roechsli/Haptic-Feedback-Robot-Controller---Master-Thesis/Reports/oechslin_june/YReport_en.pdf

# Monthly Report (Yamamoto Lab.)

date: 2018.Jul.3
Author: R. Oechslin (M2)

Research theme: Haptic Feedback Controller with Palm Pressurization

— Research Plan —

Term \Month | 2 | 3 | 4 | 5 | 6 | 7 | 8 | 9 | 10 | 11 | 12 | 1

Literature review
Design PlayStation Controller
Test PlayStation Controller
Frequency Response Analysis Design Pilot Controller
Test Pilot Controller

Theoretical Analysis
Analyze data and compare
Write Thesis

— Work Contents —

### 1 Introduction

This report is the continuation of the first two reports about the project ”Haptic Feedback Controller with Palm Pressurization”. The last report has left off with the idea of implementing a voltage follower and suggested to retake measurements to create a Bode diagram. Furthermore, it has been suggested to create an analytical model and analysis of the setup in order to run simulations to identify setup parameters such as the equivalent spring constant, gain values or motor parameters.

### 2 Theoretical analysis

To come up with a theoretical analysis of the transfer function, a simplified mechanical schematic has been drawn. This schematic can be seen in figure 1. The equations of motion can be formu-


Figure 1: Simplified mechanical schematic of the actuation system with the stimulator.

lated with the major parameters defined in the schematic. A full explanation of all parameters

– 1 – | Author: R. Oechslin

can be seen in table 2. The variables with subscript 1 refer to the first mass element, the carriage in its guideway, whereas variables with subscript 2 refer to the stimulator, also known as the palm pad. For the motor the subscript m has been used.

Designator | Explanation | Unit
Tm T θm θ LCL m1 m2 x1 x2 keq bsp n kop bop JT | Motor torque Output torque acting on carriage Motor angle Clamp link angle Clamp link length Mass of the carriage in its guideway Mass of the stimulator Position of the carriage in its guideway Position of the stimulator Equivalent spring constant Spring damping coefficient Reduction gear ratio Spring constant of the operator Damping coefficient of the operator Total inertia of mechanical setup | [Nm] [Nm] [rad] [rad] [m] [kg] [kg] [m] [m] [N/m] [Ns/m] [-] [N/m] [Ns/m] [kgm² ]

Figure 2: Setup parameters

Assumptions
First of all, it is important to mention that the transfer function is non-linear, due to the motor angle θm that determines the force acting on the carriage with mass m1. As an initial approach however, this effect has been neglected. More specifically, it is assumed that θ ≪ 1 and cos (θ)

Tm
LCL

= Fcarr becomes Tm
LCL

≃ Fcarr. Here the angle θ is the angle of the lever, pushing the carriage (ie. θm = nθ).
Furthermore, there are several types of friction in the system: the intrinsic friction within the motor and its reduction gear, inside the bearings and the carriage in its guideway. Additionally the springs have a non-negligible damping coefficient. In this work the overall friction and the spring damping have been merged and are represented by the friction coefficient bsp. The stimulator, is not in contact with the controller, but with the operator. To model the damping of the skin of the operator and the friction between the skin and the palm pad, the damping coefficient bop has been introduced. Similarly the spring constant of the operator’s skin is modeled by kop.

Spring Constant and Damping Coefficient of the Operator’s Hands
The order of magnitude of the two coefficients kop and bop are discussed in [Kuchenbecker et al., 2003] [Park et al., 2014] [Speich et al., 2005]. They all indicate parameters varying in the same order of magnitude, namely kop ≃ 400N/m and bop ≃ 5Ns/m.

Identification of the Spring Damping Coefficient
The damping coefficient of the spring bsp can be found by comparing the theoretical results of the frequency response analysis with the experimental findings. In fact, for the experimental setup, the stimulator has been fully blocked and therefore the operator’s spring coefficient can be
Author: R. Oechslin | – 2 –

seen as infinitely stiff.
By varying bsp and Bode-plotting the results of the analytical transfer function, the coefficient’s order of magnitude can be found. In order to do so, the analytical transfer function has to be identified.

Expected Transfer Functions
The system can be cut into two major transfer functions. The block diagram including these two transfer functions is depicted in figure 3.

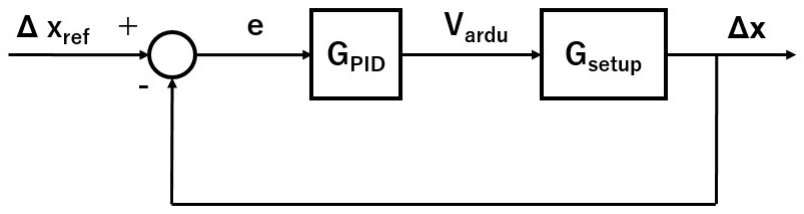
[picture p40: figure]

Figure 3: Block diagram with two different transfer functions.

According to this figure one can obtain a transfer function of the following form:

F(s) = GP ID(s)Gsetup(s) = Vardu
E

∆X

Vardu

=

∆X(s)
E(s)

(1)

where Vardu is the voltage output of the arduino for controlling the motors. Using this form one can calculate the individual transfer functions and finally relate the compression of the springs ∆x to the compression given as reference ∆xref , since ∆Xref /∆x = F/(1 + F).
PID Transfer Function The transfer function given by the PID-controller is very straightforward and can be taken out of any control theory book [Dutton et al., 1997]. Since the arduino has limited resolution with floating point operations, the error and reference has been converted into micrometers. To keep the gains consistent between the arduino code and the matlab script for analytical analysis, the multiplication factor Kµm to get from the reference distance in meters to micrometers has been introduced. Furthermore, an offset has been added (Kbit−of fset = 128) to allow for negative armature voltages and lastly the PID value has been converted to the arduino output voltage, where 255 corresponds to 5 V. The transfer function is given in equation 2.

GP ID(s) = Vardu(s)
E(s)

= (Kµm(KP +

KI
s
+ KDs) + Kbit−of fset)KP ID2V ardu | (2)

Finally, there is also the gain of the amplifier in voltage mode, which converts the voltage of the arduino into the voltage applied to the motors. This gain is Kampl = 10Volt/Volt. To this voltage an offset voltage of Vof fset = −25V is added.

Motor Equations The second transfer function relates the motor torque Tm to the arduino voltage as well as the output ∆x to Tm. Due to the back electromotive force these two parts are related and have to be treated as a whole.
The output torque Tm of the motor can be calculated using the sum of all torques and the conversion parameters intrinsic to the motor.
Similar to the setup and analysis in [Junior et al., 2016] the equations of the motor are given as:

La

dia
dt + Raia + Kemf ˙θm = Va | (3)

where La is the armature inductance, Ra the armature resistance and ia the armature current of the motor. Kemf is the back electromotive force constant also given by the motor. Va is the armature voltage and θm is the angle of the motor shaft.
Furthermore, with Newton’s law, the sum of all torques must be zero, or:

JT

¨θm −

keqLCL
n

∆x −

bspLCL
n
( ˙x2 − x˙ 1) = Tm = Kτ ia | (4)

In equation 4 the parameter JT stands for the total equivalent inertia of the motor, the clamping link and the carriage of mass m1. Kτ is the proportional current torque gain constant. The moment of inertia can either be calculated as the sum of all inertias seen by the motor shaft, or measured in a simple test.

Analytical Inertia Identification
The total inertia of the system is determined by the inertia of the rotor and gears Jm, the inertia of the clamp link JCL as well as the inertia of the carriage assembly with mass m1. The last one can be found by simplifying the load to a point mass at distance of the clamp link’s length LCL, which yields a moment of inertia of Jcarr = m1L

2
CL. The gear box affects the inertia seen by the motor shaft by the square of its ratio n:

Jref lected =

Jload
n²

(5)

We therefore have a total inertia of:

JT = Jm +

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
where JCL can be calculated by approximating it as a cantilever with an off-center axis of distance LCL/2

1
:

JCL =

1
12

mCL(A

2 + B

2 + 12l

2
) | (7)

where A and B are the width and length respectively.
The calculated total moment of inertia for the motor with a reduction ration of n = 112 is JT = 6.87 × 10−8
kgm²

Experimental Inertia Identification
Alternatively, one can approximate the total moment of inertia by applying a constant current on the motor and measuring the acceleration. In this case the traveled distance has been derivated twice to find the acceleration, which results in an amplification of errors. Furthermore, the constant current has been kept very low, (between 20 and 100 mA), which led to a slow movement and therefore higher friction impact on the measurements. However, the results are consistent with the theoretically calculated values:

JT =

7.5 × 10−4
n²

= 5.98 × 10−8
kgm²

Relating ∆X to θ

1
(2018, June 19th) retrieved from http://www.orientalmotor.com/technology/motor-sizing-calculations. html

The conversion between the angle θ and the carriage’s traveled distance x1 can be found by assuming that the horizontal displacement of the carriage is given by LCLsin(θ) = x1. For small angles of θ the Taylor expansion gives:

LCLθ ≃ x1 | (8)

The output ∆x is the compression of the springs and is given by ∆x = x2 − x1. For finding x2

the equation of motion given by Newton’s law has been considered.

m2x¨2 = −keq(x2 − x1) − bsp( ˙x2 − x˙ 1) − kopx2 − bopx˙ 2 | (9)

In the case where the stimulator has been blocked by a wall, ˙x2 has been forced to zero. Using the Laplace transform and equation 9 one finds the expression of x2:

X2 = −

keq + bsps
s

2m2 + bops + kop

∆X | (10)

Motor and Spring Transfer Function Combining all the equations one can find the final block diagram, which can be seen in figure 4

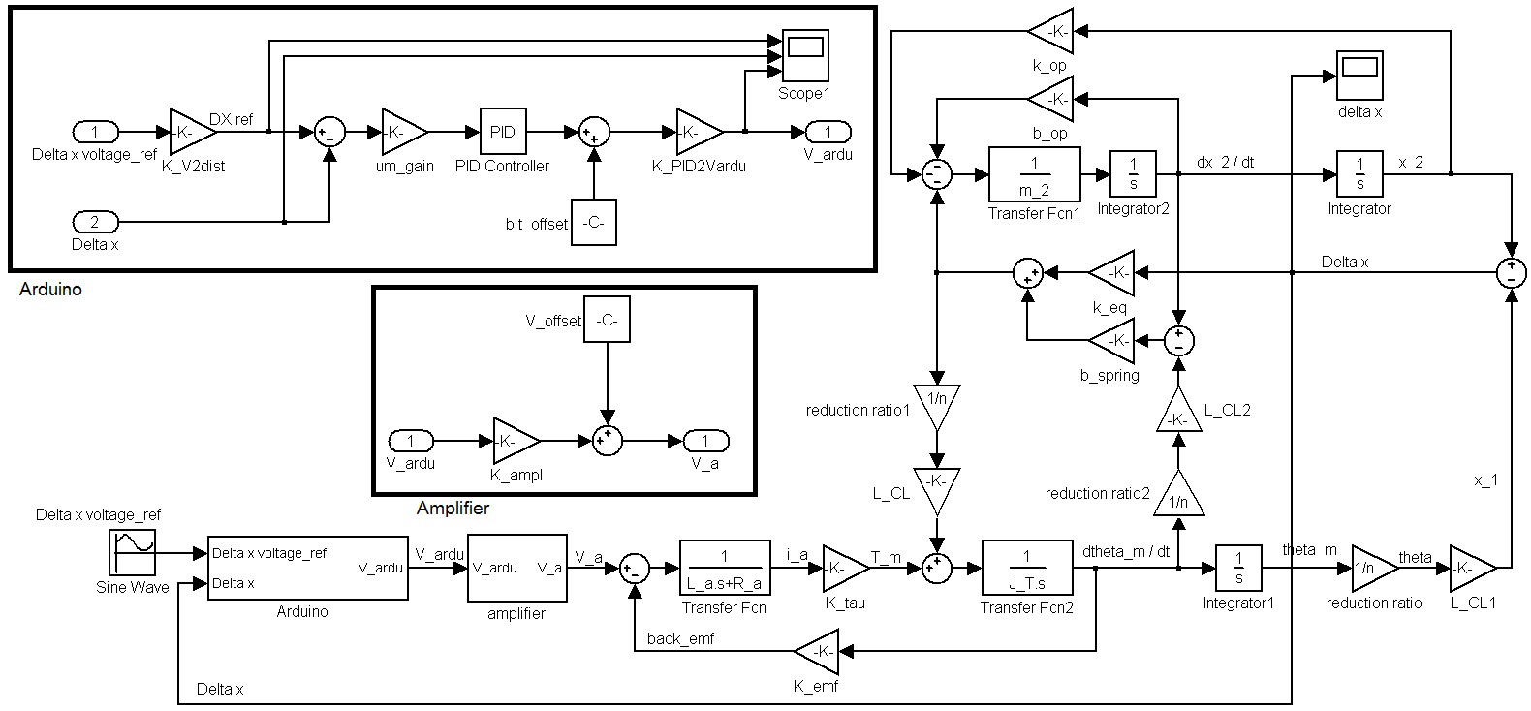
[picture p41: figure]

Figure 4: Complete block diagram relating the output ∆x to the input ∆xref .

From this diagram and the equations mentioned above, one can obtain the transfer functions that relate the output ∆x and input ∆xref as introduced in equation 1, where ∆X(s) and ∆Xref (s) are the Laplace transforms of the output and input functions respectively.
It is thus possible to study the frequency response by simulating this setup with the assumptions mentioned earlier.

Main Equations for Analytical Transfer Function

∆Xref − ∆X = E | (11)

((KP + KDs +

KI
s
)EKµm + Kbit−of fset)KP ID2V arduKampl + Vof fset = Va | (12)

Va − Kemf ˙θm

Las + Ra

Kτ + Fcoupled = JT

¨θm | (13)

Fcoupled = (keq + bsps)

LCL
n
∆X | (14)

θm =

n

LCL

X1 = −

n

LCL

(1 + keq + bsps
m2s

2 + bops + kop

)∆X | (15)

Note that the constant offsets in equation 12 are for pure symmetrical reasons and will cancel each other out, since Kbit−of fsetKP ID2V arduKampl +Vof fset = 0 and the equation becomes ((KP + KDs +

KI
s

)EKµm)KP ID2V arduKampl = Va. This is the equivalent to a standard PID form with gains K′
P

, K′

D and K′
I
In the case of the experimental setup the palm pad has been blocked and therefore x2 has been forced to be constant. The last equation becomes thus: θm = −

n
LCL

∆X.

Tracking Behavior of the P-controller
The tracking behavior of the P-controlled setup can be seen in the following figures.


Figure 5: Tracking behavior of the P-controller for 2 Hz.

Comparison of Results - P-controller and Experimental Data
The analytical transfer function has only been calculated for a specific set of spring damping coefficients bsp. The results for the uniformly spaced values between 100Ns/m and 400Ns/m are depicted in figure 7. The gains that have been used are for a P-controller, it was namely K′
P = 39.2

V
mm

. The simulation result that was closest to the experimental setup can be seen in figure 8 and the corresponding transfer function is:

∆X

∆Xref

=

1.23 × 10³
3.24 × 10−6s

3 + 6.67 × 10−2s
2 + 8.48s + 1.23 × 10³

(16)

As it can be seen in figure 8 there is a constant gain of 1 for lower frequencies and a slight resonance top becomes visible around 18Hz. The phase shift is of around −210◦
for the tested


Figure 6: Tracking behavior of the P-controller for 10 Hz.


Figure 7: Bode plot comparison of experimental data of the P-controller and analytical transfer functions for several different bsp.

frequencies, and the lag does not increase more than 45◦
for the frequencies of interest. Due to the setup constraints, the analytical results of higher frequencies have not been considered.

Motor Comparison

When one goes back to the experimental results where the two motors with different reduction gear ratios have been compared (previous report), one can conclude that the motor with the higher reduction ratio has a higher output force with a tradeoff of speed. Since one of the critical elements of the SEA system is its actuation speed, it is essential to push the boundaries as far as possible. However, the high gain frequency response in the experimental setup starts to drop at much higher frequencies than the actual operating frequency (which is given by the rather slow communication speed between the robot and the control device of fop ≃ 2 − 5 Hz).

Due to the fact that even with the stronger reduction gear motor, the springs cannot be compressed


Figure 8: Bode plot comparison of experimental data of the P-controller and analytical transfer function for bsp = 300Ns/m.

to their limits, a higher possible output force has been favored and therefore the stronger motor seems more appropriate.

Experimental PID Tuning

At first, the Ziegler Nichols tuning method has been used to identify the PID gains for the setup. However, due to the non-linear behaviour, these gains resulted in a rather poor tracking performance of the reference signal.
Since an educated tuning of the gains is the very core problem of all control engineering, a lot of different approaches exist to find optimal or sub-optimal gain values. Given the complexity of the setup, it seemed reasonable to go for the simple trial and error approach, where the gains have been tuned and the tracking performance was shown in real-time. This approach led to the following gain coefficients:
Designator | Value | Unit
K′ P K′ I K′ D | 47.6 0.124 247 | [V/mm] [V/mm/s] [Vs/mm]

Figure 9: Trial and error PID tuning.

Tracking Behavior of the PID-controller

The tracking behavior of the P-controlled setup can be seen in the following figures.

Comparison of Results - PID-controller and Experimental Data

With the gains stated in table 9, the frequency response can be measured again. This has been done for the left and right side, both using the motor with a reduction ratio of n = 112. The comparison between the analytical results from the mathematical model and the experimentally gathered data can be seen in figure 12.

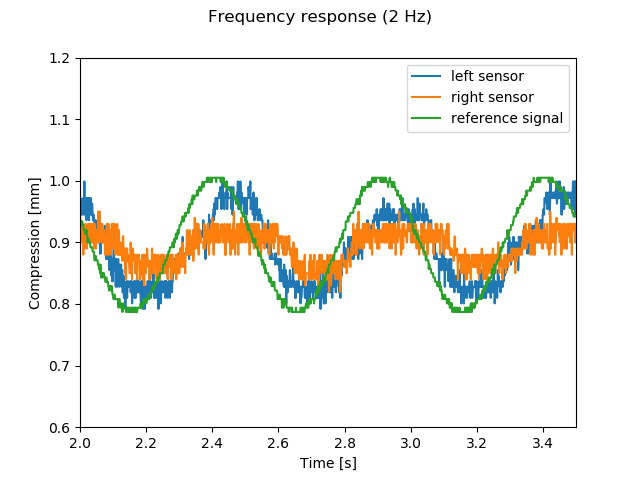
[picture p42: figure]

Figure 10: Tracking behavior of the PID-controller for 2 Hz.

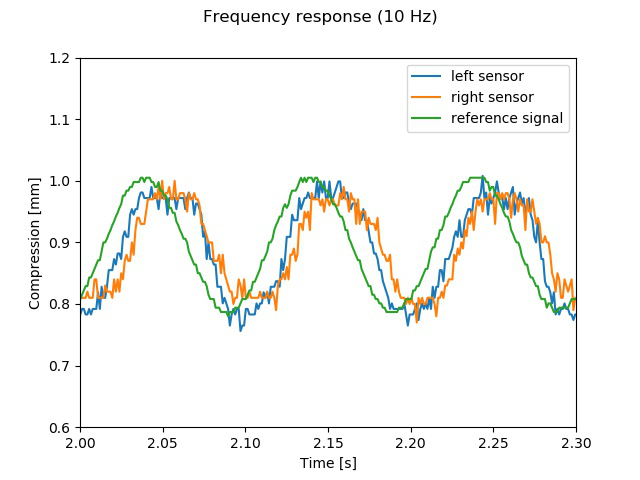
[picture p43: figure]

Figure 11: Tracking behavior of the PID-controller for 10 Hz.

### 3 Discussion

P-controlled Device
As figure 8 indicates, the results of the mathematical model seems to correspond with the experimental data. Furthermore, a damping coefficient of bsp = 300 Ns/m could be identified. The tracking behavior of this P-controller was reasonable for lower frequencies, even though there was a slight steady-state offset. The constant phase-lag was very small for small frequencies and did not exceed 45◦
for frequencies up to 10 Hz. Even an approach of discretizing the analytical results did not yield a better match of the results.

PID-controlled Device
When the PID-controller has been implemented, the difference between analytical results and the experiments was much bigger. First it was noteworthy, that the two motors showed a different behavior with the same gains. This might stem from several asymmetries in the setup. First of


Figure 12: Bode plot comparison of experimental data of the PID-controller and analytical transfer function for bsp = 100Ns/m.

all and most importantly, the distance sensors are different, and have different threshold values. Also, the springs might not have been glued in a perfectly symmetrical manner. However, the noise characteristics of the sensors are in a similar order of magnitude and do not account for the differences here. Lastly, there are the mechanical aspects of how the motors have been screwed to the controller. Due to the high-frequency driving, the screws loosen from time to time, which can have a significant impact on the Bode plots. Furthermore, there might be a slight misalignment of the motor shaft axis and the guideway, which results in an opposing force.
Again, the discretization of the analytical transfer function did not yield a better match between the analytical and experimental data.
Judging from the frequency response seen in figure 12 the tracking is relatively bad at low frequencies, not only because there is an attenuation, but also that the resonance top at higher frequencies quickly leads to saturation of the applicable motor voltage. In addition to this, the phase lag is much bigger and is already at least 45◦
in the lower range of the bandwidth. This is due to the filters that have been used. The first filter is an RC-circuit that takes the PWM signal from the arduino and produces a more continuous voltage signal for the amplifiers. The cut-off frequency is 330 Hz. The second filter is within the arduino code and is used to filter the measured distance. This filter was necessary to reduces the impact of noise amplification in the derivative part of the PID-controller. Three different filters with cut-off frequencies from f1 = 1.6 Hz, f2 = 4.2 Hz and f3 = 8.8 Hz have been tested.

### 4 Conclusion

Given the results for the P-controller, one can assume that the mathematical model is correct. However, when one implements a PID-controller, a higher discrepancy between mathematical model and experimental data arises. Even though the parameters used in the mathematical model have been double-checked (such as the moment of inertia for example), its validity can be questioned.
From the two different implementations, the P-controller shows a better tracking behavior for the operational bandwidth.

### 5 Outlook

In the future, the P- and PID-controller shall be tested and a subjective measure of the feedbacks smoothness and transparency shall be reported.
A more thorough literature shall be done to discuss the findings with existing papers.
A design-choice guide shall be created in order to facilitate future research for similar setups.

References

[Dutton et al., 1997] Dutton, K., Thompson, S., and Barraclough, B. (1997). The art of control engineering. Addison Wesley Harlow.

[Junior et al., 2016] Junior, A. G. L., de Andrade, R. M., and Bento Filho, A. (2016). Series elastic actuator: Design, analysis and comparison. In Recent Advances in Robotic Systems. InTech.

[Kuchenbecker et al., 2003] Kuchenbecker, K. J., Park, J. G., and Niemeyer, G. (2003). Characterizing the human wrist for improved haptic interaction. In ASME 2003 International Mechanical Engineering Congress and Exposition, pages 591–598. American Society of Mechanical Engineers.

[Park et al., 2014] Park, J., Paˇzin, N., Friedman, J., Zatsiorsky, V. M., and Latash, M. L. (2014). Mechanical properties of the human hand digits: Age-related differences. Clinical Biomechanics, 29(2):129–137.

[Speich et al., 2005] Speich, J. E., Shao, L., and Goldfarb, M. (2005). Modeling the human hand as it interacts with a telemanipulation system. Mechatronics, 15(9):1127–1142.
