roechsli/Haptic-Feedback-Robot-Controller---Master-Thesis/3D designs/Game Controller/figures/PS_controller_smaller.jpg

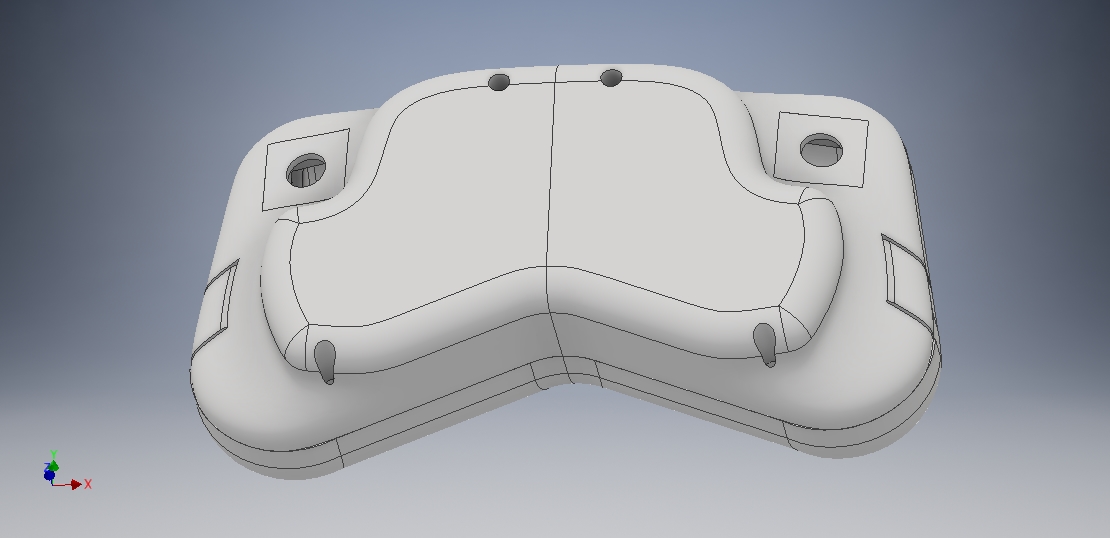
3D designs/Game Controller/figures/PS_controller_smaller.jpg
