roechsli/Haptic-Feedback-Robot-Controller---Master-Thesis/3D designs/Yoke Controller/figures/left_hand_joystick_cam_open_rend.jpg

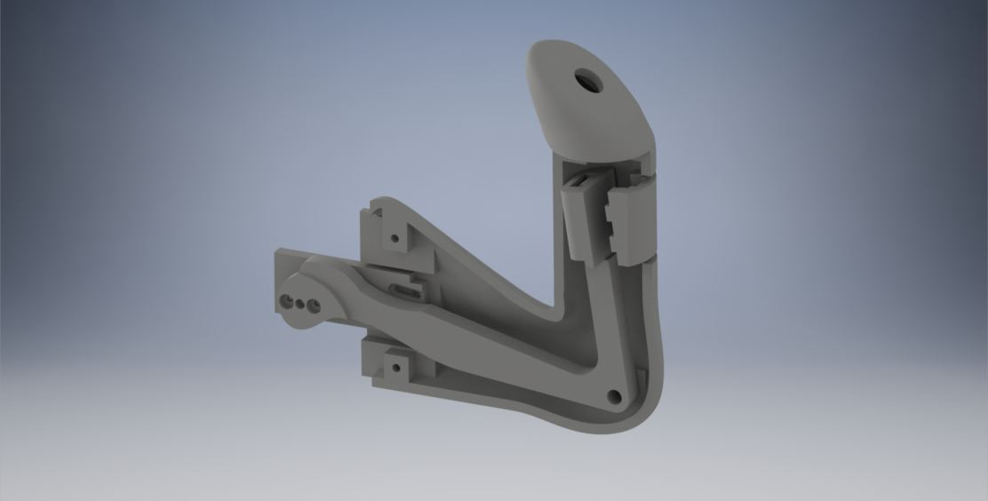
3D designs/Yoke Controller/figures/left_hand_joystick_cam_open_rend.jpg
