roechsli/Haptic-Feedback-Robot-Controller---Master-Thesis/Data/frequency_response/20180525_fra_logs/figs/f2/2plot_zoom.jpg

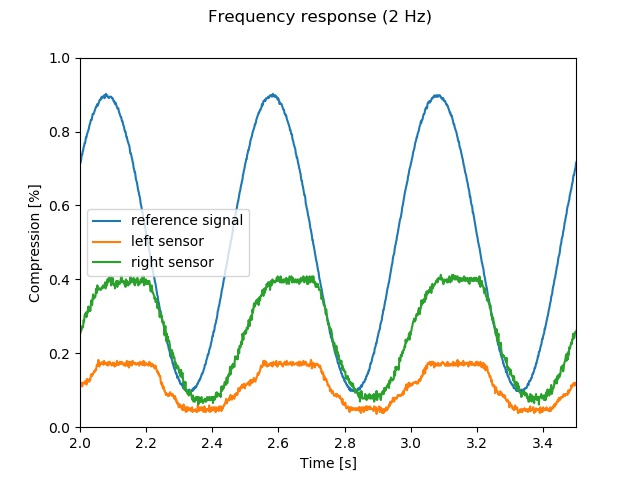
Data/frequency_response/20180525_fra_logs/figs/f2/2plot_zoom.jpg
