roechsli/Haptic-Feedback-Robot-Controller---Master-Thesis/Data/frequency_response/20180525_fra_logs/figs/f6.3/6.3plot_zoom_fixed_time.jpg

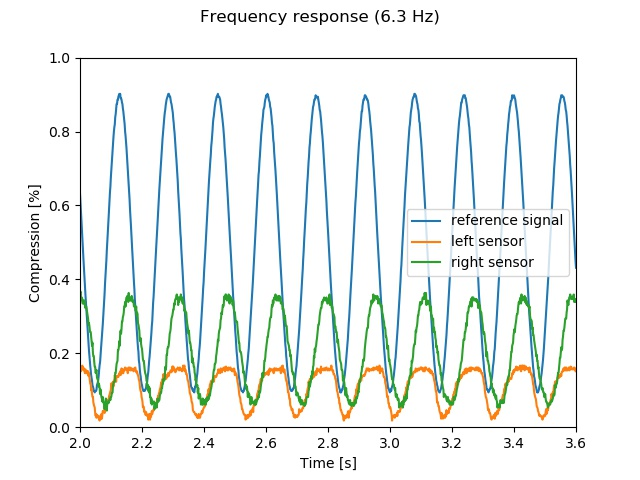
Data/frequency_response/20180525_fra_logs/figs/f6.3/6.3plot_zoom_fixed_time.jpg
