roechsli/Haptic-Feedback-Robot-Controller---Master-Thesis/Data/frequency_response/20180529_fra_logs/figs/f1.6/1.6plot_zoom.jpg

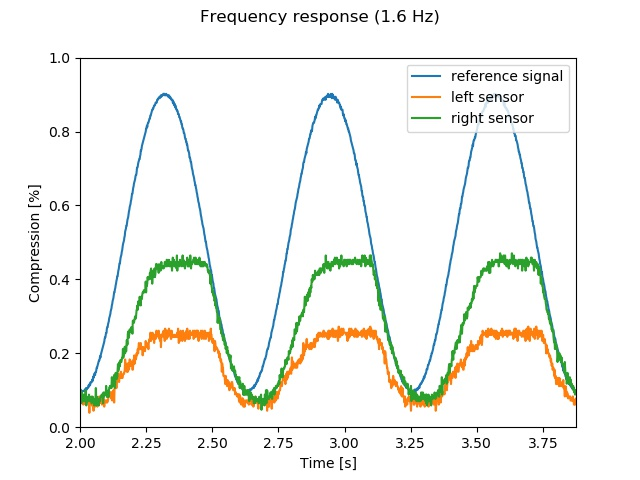
Data/frequency_response/20180529_fra_logs/figs/f1.6/1.6plot_zoom.jpg
