roechsli/Haptic-Feedback-Robot-Controller---Master-Thesis/Data/frequency_response/20180529_fra_logs/figs/f16/16plot_zoom.jpg

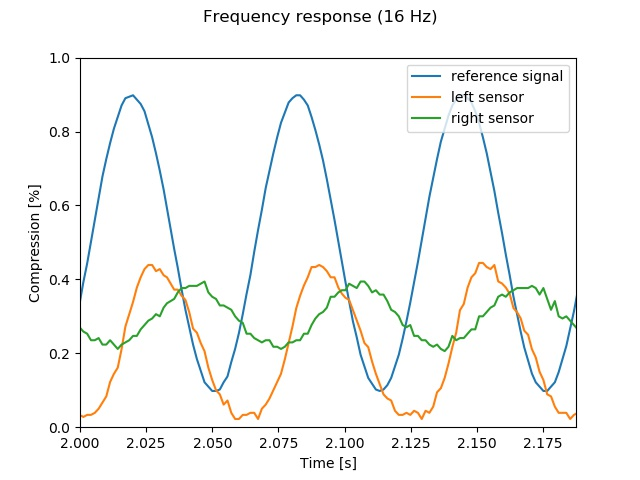
Data/frequency_response/20180529_fra_logs/figs/f16/16plot_zoom.jpg
