roechsli/Haptic-Feedback-Robot-Controller---Master-Thesis/Data/frequency_response/20180621_fra_logs/figs/bode_right.jpg

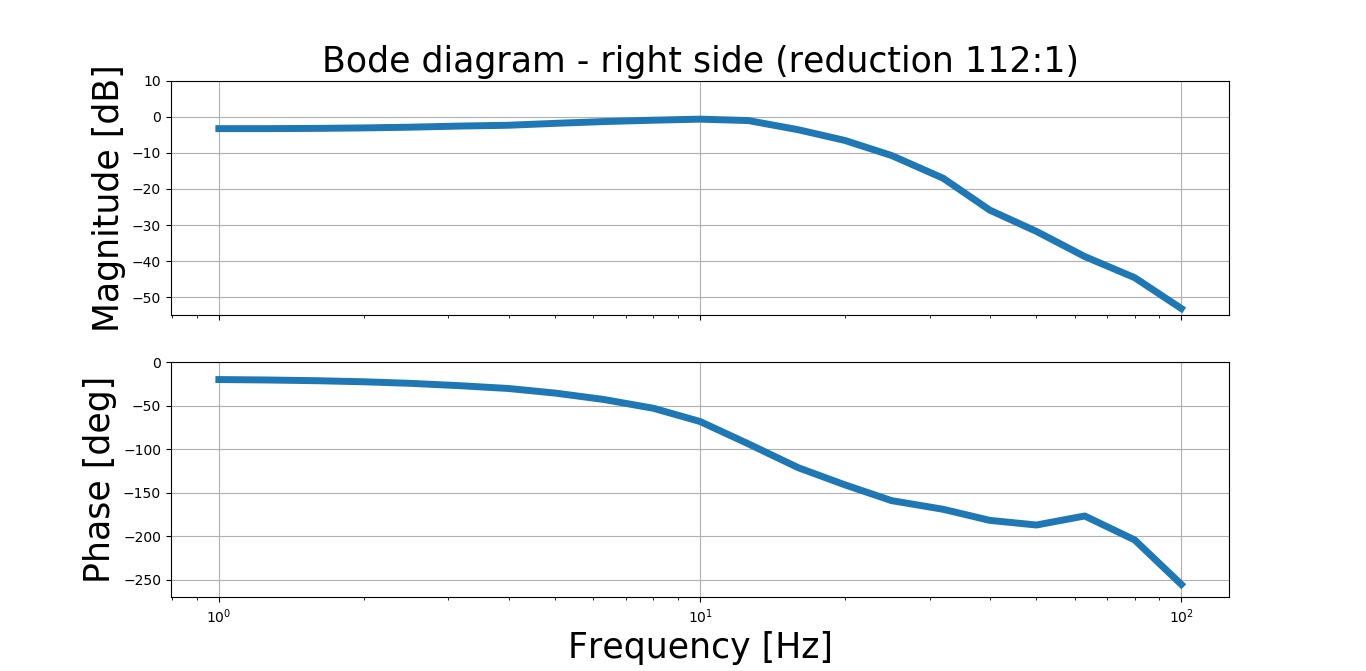
Data/frequency_response/20180621_fra_logs/figs/bode_right.jpg
