roechsli/Haptic-Feedback-Robot-Controller---Master-Thesis/Data/frequency_response/20180621_fra_logs/figs/f32/32plot_zoom_fixed_time.jpg

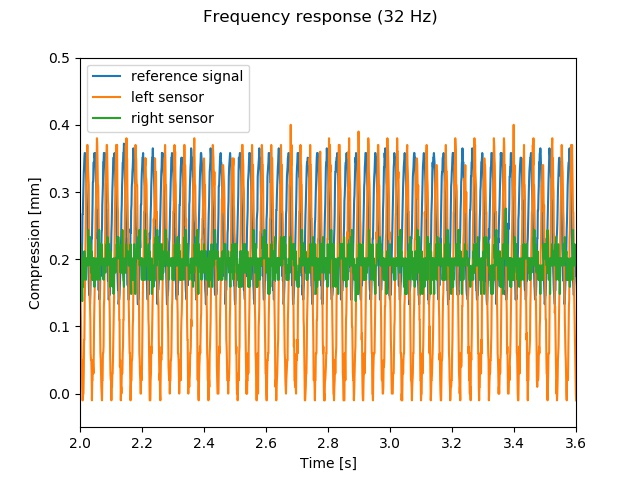
Data/frequency_response/20180621_fra_logs/figs/f32/32plot_zoom_fixed_time.jpg
