roechsli/Haptic-Feedback-Robot-Controller---Master-Thesis/Data/frequency_response/20180621_fra_logs/figs/f80/80plot_zoom_fixed_time.jpg

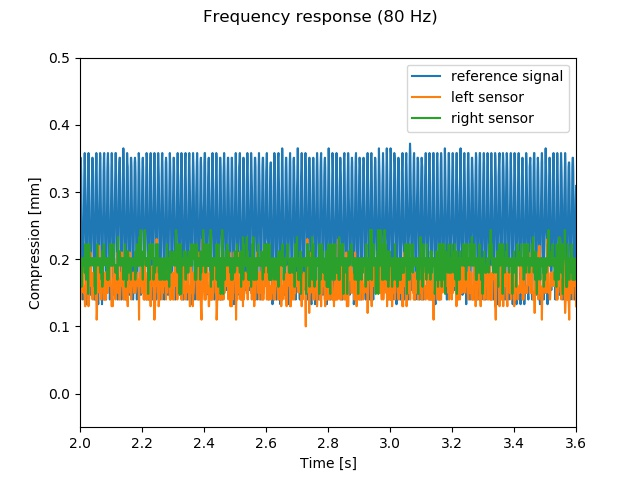
Data/frequency_response/20180621_fra_logs/figs/f80/80plot_zoom_fixed_time.jpg
