roechsli/Haptic-Feedback-Robot-Controller---Master-Thesis/Data/frequency_response/20180626_fra_logs_pid_impl/figs/f1.6/1.6plot_zoom.jpg

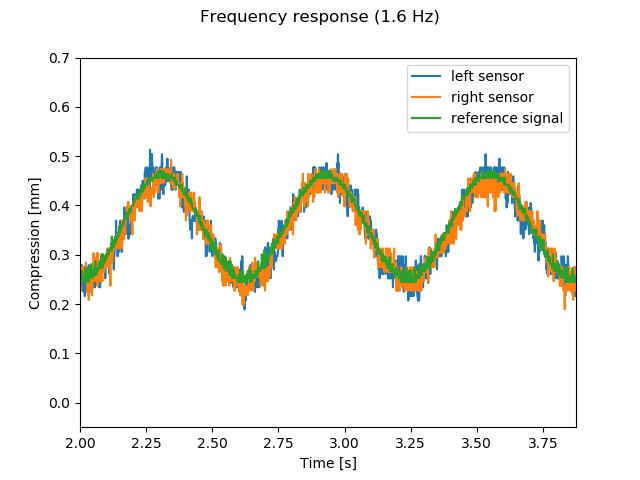
Data/frequency_response/20180626_fra_logs_pid_impl/figs/f1.6/1.6plot_zoom.jpg
