roechsli/Haptic-Feedback-Robot-Controller---Master-Thesis/Data/frequency_response/20180626_fra_logs_pid_impl/figs/f3.17/3.17plot_zoom.jpg

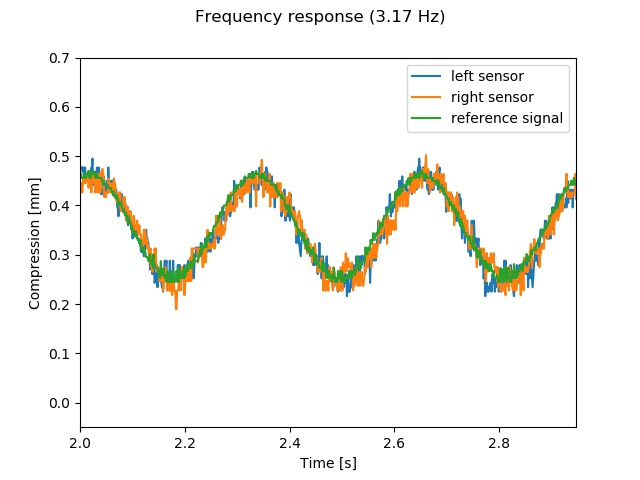
Data/frequency_response/20180626_fra_logs_pid_impl/figs/f3.17/3.17plot_zoom.jpg
