roechsli/Haptic-Feedback-Robot-Controller---Master-Thesis/Data/frequency_response/20180626_fra_logs_pid_impl/figs/f4/4plot_zoom.jpg

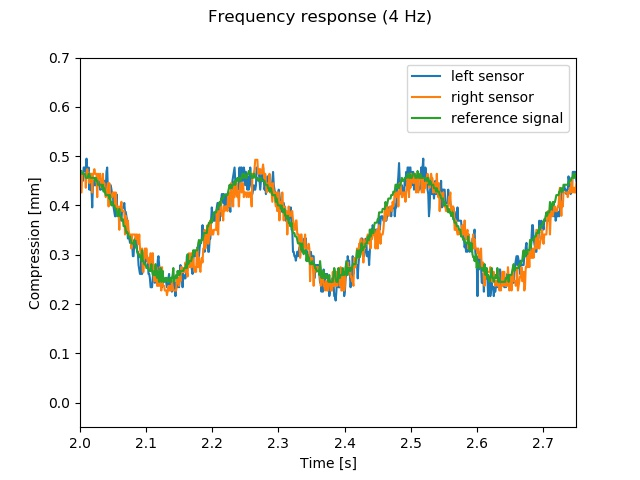
Data/frequency_response/20180626_fra_logs_pid_impl/figs/f4/4plot_zoom.jpg
