roechsli/Haptic-Feedback-Robot-Controller---Master-Thesis/Data/frequency_response/20180626_fra_logs_pid_impl/figs/f12.6/12.6plot_zoom_fixed_time.jpg

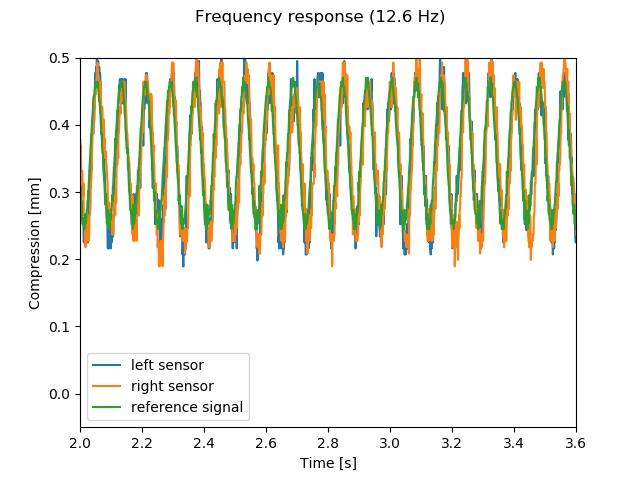
Data/frequency_response/20180626_fra_logs_pid_impl/figs/f12.6/12.6plot_zoom_fixed_time.jpg
