roechsli/Haptic-Feedback-Robot-Controller---Master-Thesis/Data/frequency_response/20180626_fra_logs_pid_impl/figs/f32/32plot_zoom_fixed_time.jpg

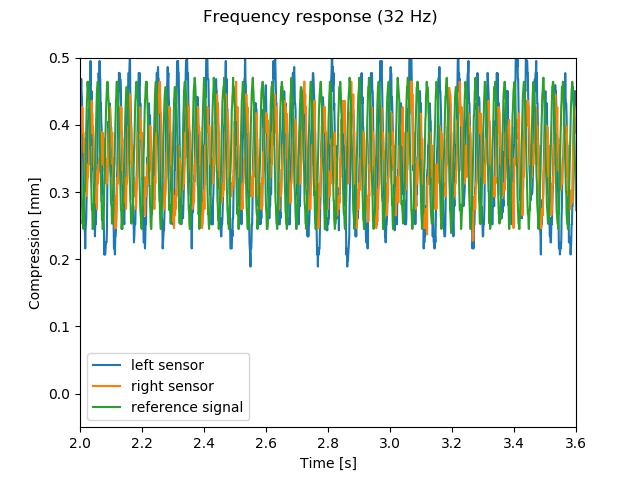
Data/frequency_response/20180626_fra_logs_pid_impl/figs/f32/32plot_zoom_fixed_time.jpg
