roechsli/Haptic-Feedback-Robot-Controller---Master-Thesis/Data/frequency_response/20180629_fra_logs_p_02/figs/bode_both.jpg

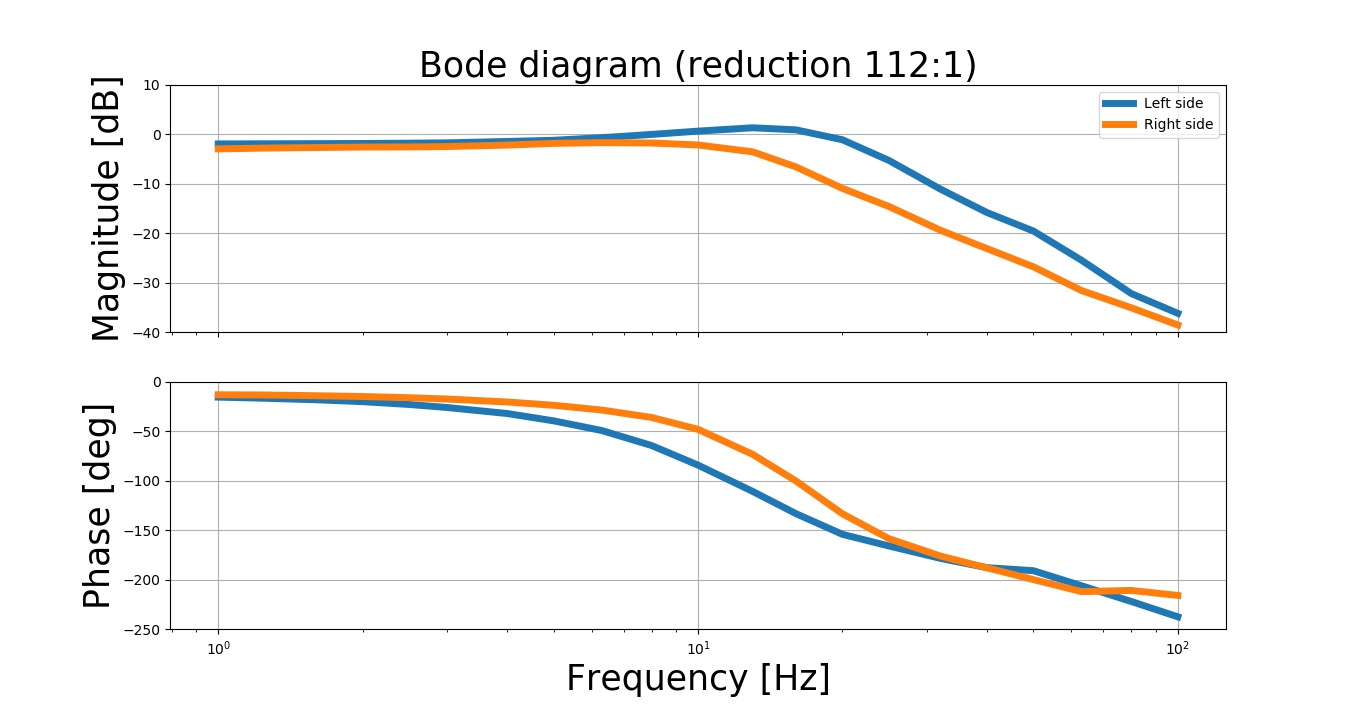
Data/frequency_response/20180629_fra_logs_p_02/figs/bode_both.jpg
