roechsli/Haptic-Feedback-Robot-Controller---Master-Thesis/Data/frequency_response/20180629_fra_logs_p_02/figs/f10/10plot_zoom_fixed_time.jpg

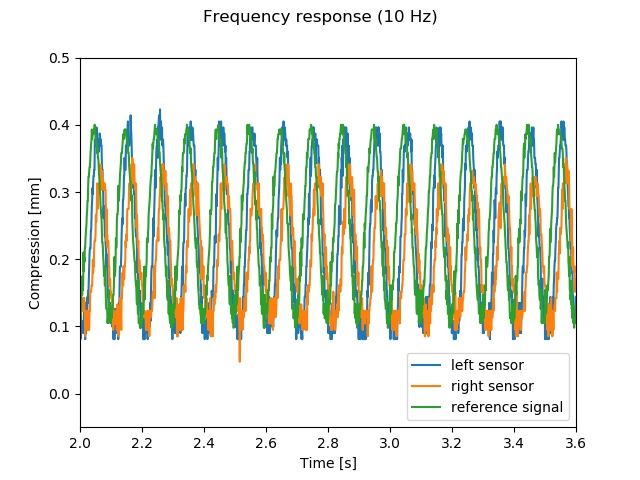
Data/frequency_response/20180629_fra_logs_p_02/figs/f10/10plot_zoom_fixed_time.jpg
