roechsli/Haptic-Feedback-Robot-Controller---Master-Thesis/Data/frequency_response/20180629_fra_logs_p_02/figs/f25/25plot_zoom_fixed_time.jpg

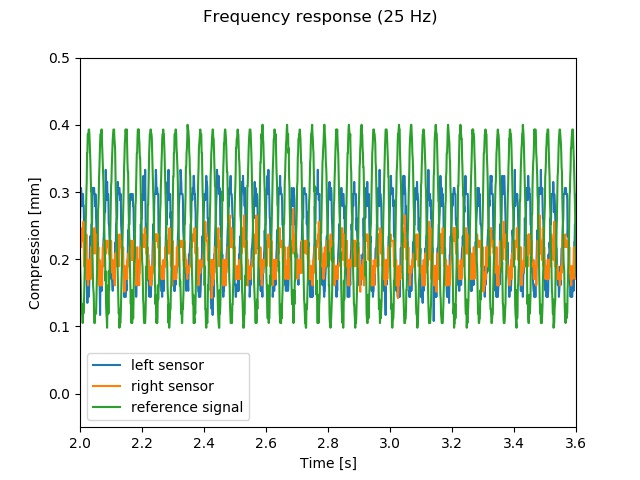
Data/frequency_response/20180629_fra_logs_p_02/figs/f25/25plot_zoom_fixed_time.jpg
