roechsli/Haptic-Feedback-Robot-Controller---Master-Thesis/Data/frequency_response/20180629_fra_logs_p_02/figs/f80/80plot_zoom.jpg

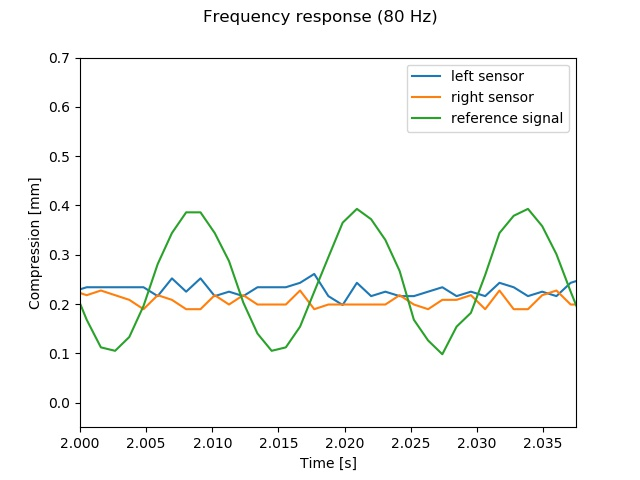
Data/frequency_response/20180629_fra_logs_p_02/figs/f80/80plot_zoom.jpg
