roechsli/Haptic-Feedback-Robot-Controller---Master-Thesis/Data/frequency_response/20180703_fra_logs_PID_243_63_00126/figs/bode_right_pid.jpg

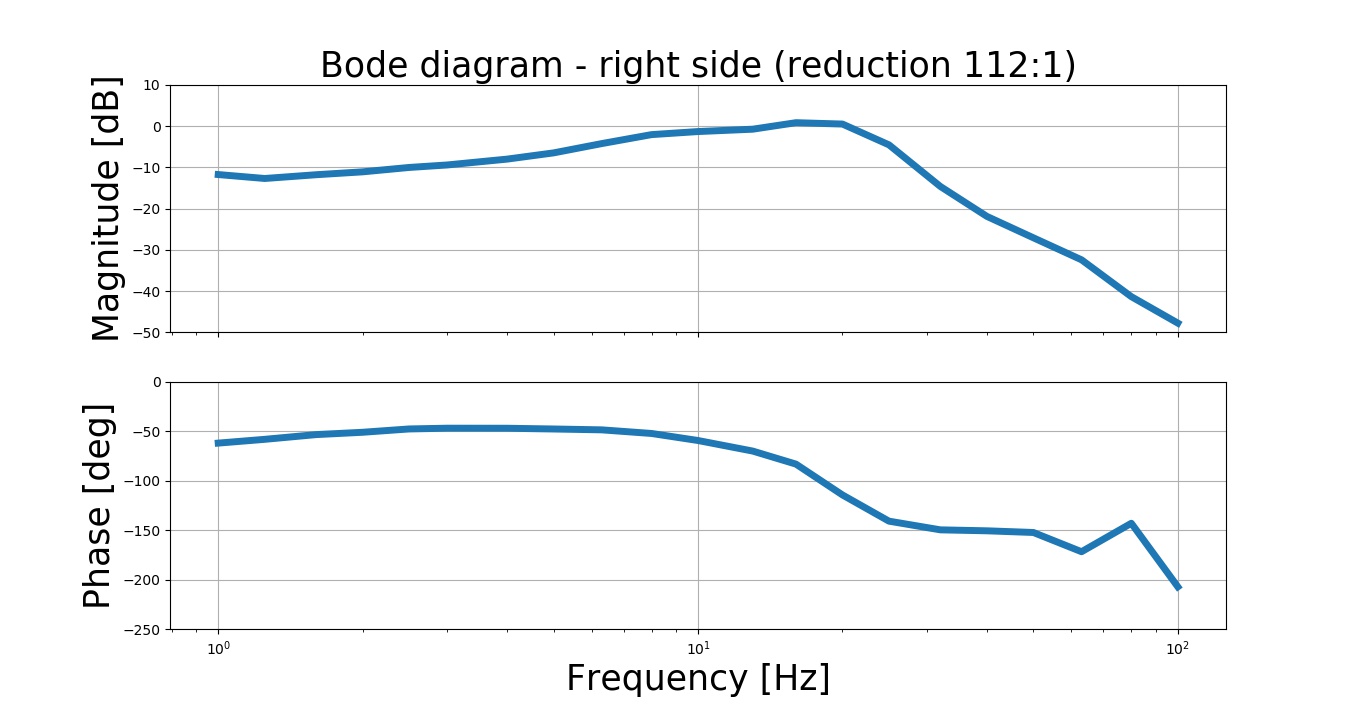
Data/frequency_response/20180703_fra_logs_PID_243_63_00126/figs/bode_right_pid.jpg
