roechsli/Haptic-Feedback-Robot-Controller---Master-Thesis/Data/frequency_response/20180704_fra_logs_PID_243_63_00126/figs/f8/8plot_zoom_fixed_time.jpg

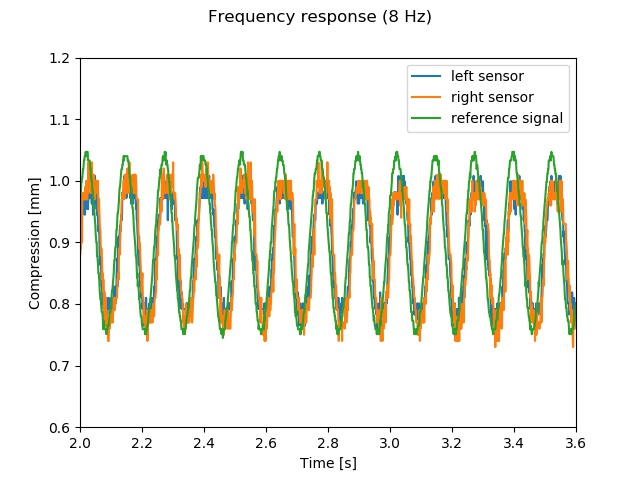
Data/frequency_response/20180704_fra_logs_PID_243_63_00126/figs/f8/8plot_zoom_fixed_time.jpg
