roechsli/Haptic-Feedback-Robot-Controller---Master-Thesis/Data/frequency_response/20180704_fra_logs_PID_243_63_00126_10perc/figs/f1.25/1.25plot_zoom.jpg

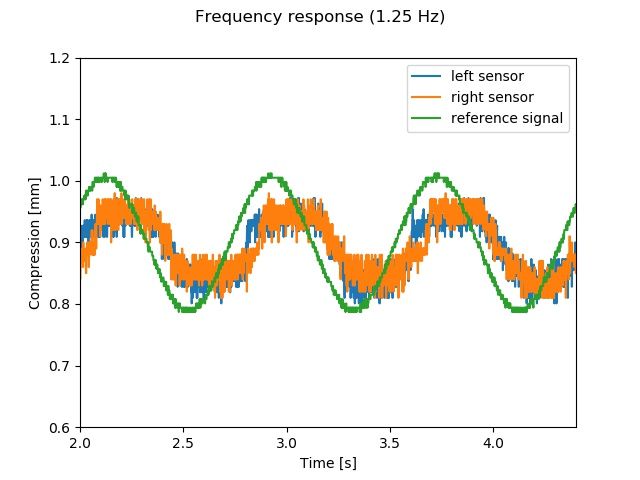
Data/frequency_response/20180704_fra_logs_PID_243_63_00126_10perc/figs/f1.25/1.25plot_zoom.jpg
