roechsli/Haptic-Feedback-Robot-Controller---Master-Thesis/Data/frequency_response/20180719_fra_logs_pilot_P02/figs/f5/5plot_zoom_fixed_time.jpg

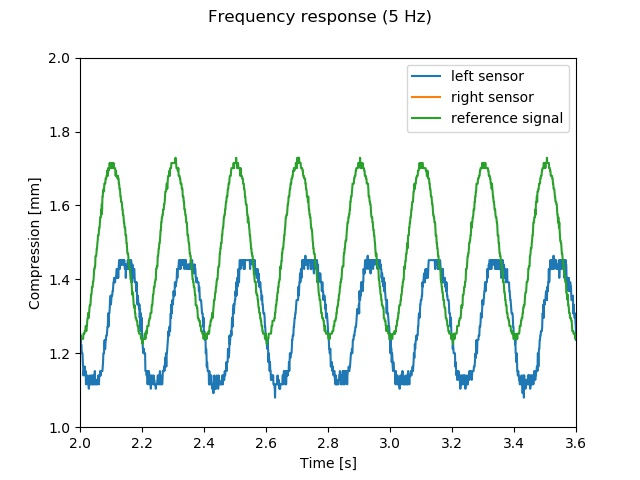
Data/frequency_response/20180719_fra_logs_pilot_P02/figs/f5/5plot_zoom_fixed_time.jpg
