roechsli/Haptic-Feedback-Robot-Controller---Master-Thesis/Data/frequency_response/20180719_fra_logs_pilot_P02/figs/f6.3/6.3plot_zoom_fixed_time.jpg

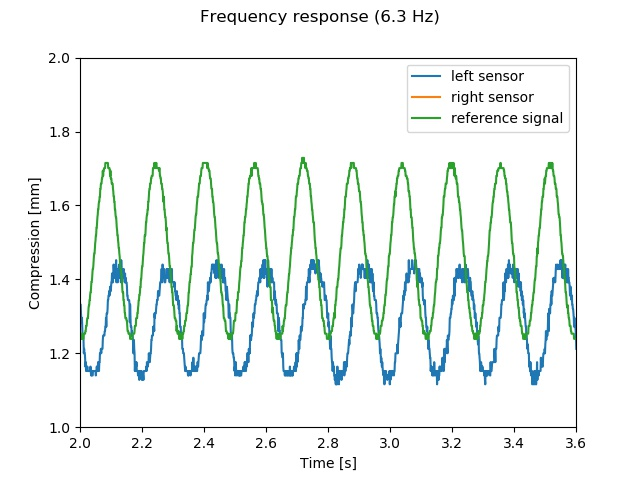
Data/frequency_response/20180719_fra_logs_pilot_P02/figs/f6.3/6.3plot_zoom_fixed_time.jpg
