roechsli/Haptic-Feedback-Robot-Controller---Master-Thesis/Data/frequency_response/20180719_fra_logs_pilot_P02/figs/f32/32plot_zoom.jpg

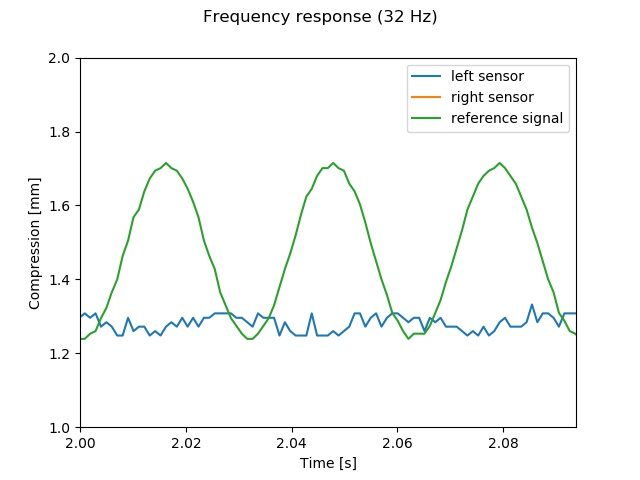
Data/frequency_response/20180719_fra_logs_pilot_P02/figs/f32/32plot_zoom.jpg
