roechsli/Haptic-Feedback-Robot-Controller---Master-Thesis/Data/frequency_response/20180726_fra_logs_pilot_P01_saturated2/figs/f6.3/6.3plot_zoom.jpg

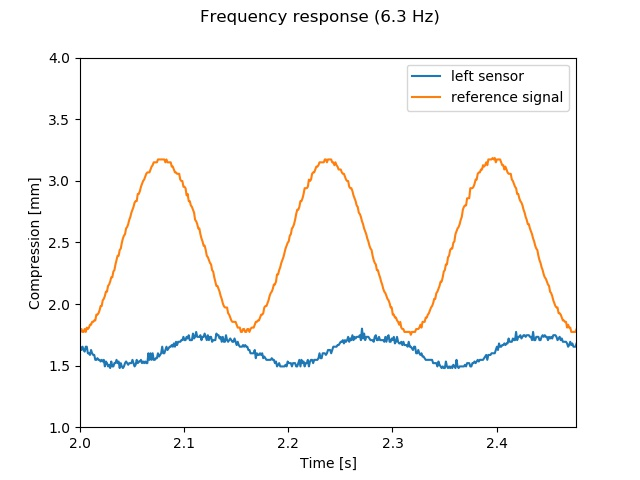
Data/frequency_response/20180726_fra_logs_pilot_P01_saturated2/figs/f6.3/6.3plot_zoom.jpg
