roechsli/Haptic-Feedback-Robot-Controller---Master-Thesis/Data/frequency_response/20180726_fra_logs_pilot_P01_saturated2/figs/f13/13plot_zoom_fixed_time.jpg

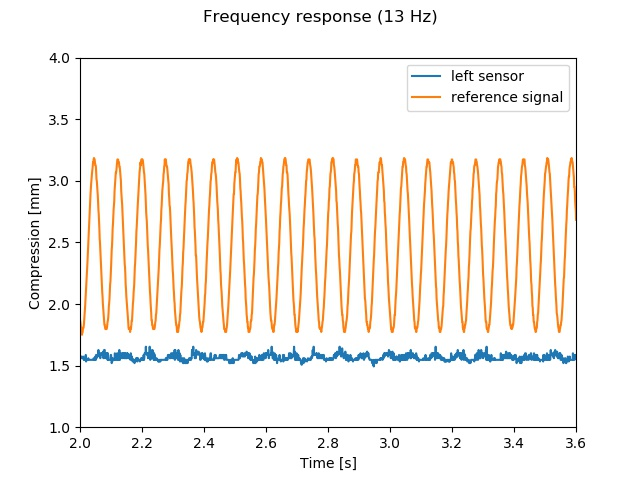
Data/frequency_response/20180726_fra_logs_pilot_P01_saturated2/figs/f13/13plot_zoom_fixed_time.jpg
