roechsli/Haptic-Feedback-Robot-Controller---Master-Thesis/Data/frequency_response/20180726_fra_logs_pilot_P01_saturated/figs/f2.5/2.5plot_zoom.jpg

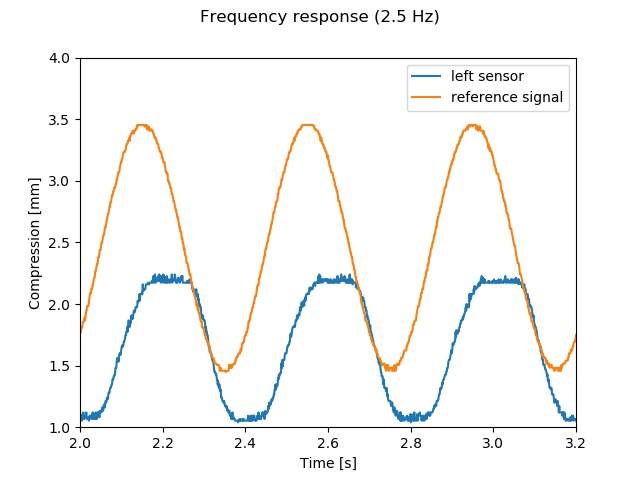
Data/frequency_response/20180726_fra_logs_pilot_P01_saturated/figs/f2.5/2.5plot_zoom.jpg
