roechsli/Haptic-Feedback-Robot-Controller---Master-Thesis/Data/frequency_response/20180727_fra_logs_pilot_P10Vmm/figs/f8/8plot_zoom.jpg

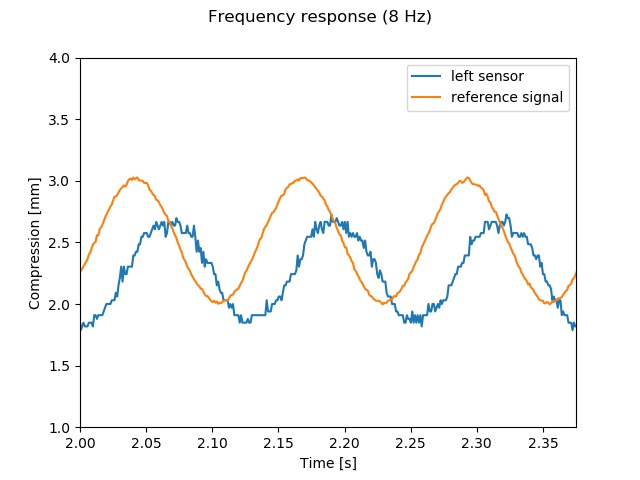
Data/frequency_response/20180727_fra_logs_pilot_P10Vmm/figs/f8/8plot_zoom.jpg
