roechsli/Haptic-Feedback-Robot-Controller---Master-Thesis/Data/frequency_response/20180727_fra_logs_pilot_P10Vmm/figs/f16/16plot_zoom_fixed_time.jpg

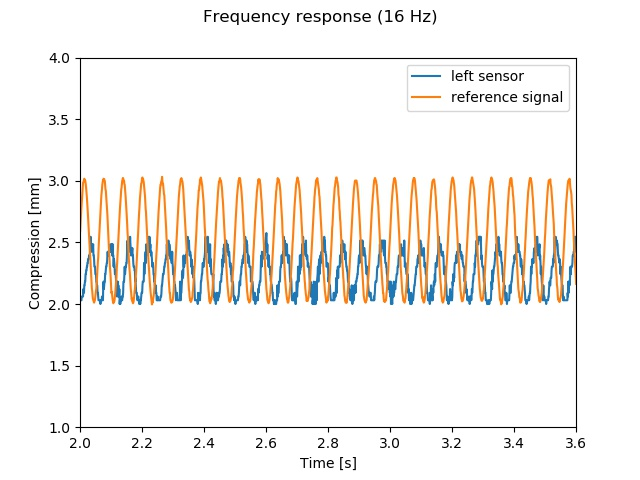
Data/frequency_response/20180727_fra_logs_pilot_P10Vmm/figs/f16/16plot_zoom_fixed_time.jpg
