roechsli/Haptic-Feedback-Robot-Controller---Master-Thesis/Data/frequency_response/ardu_ref_plots/figs/all_in_one.jpg

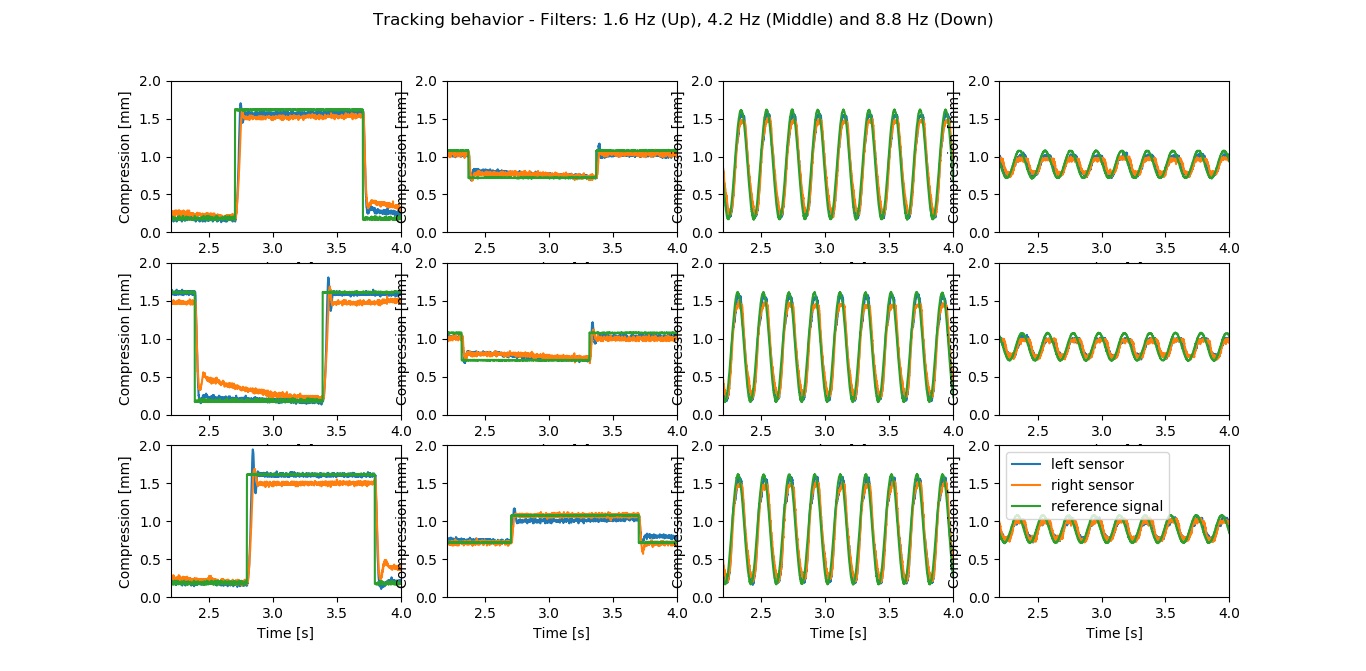
Data/frequency_response/ardu_ref_plots/figs/all_in_one.jpg
