roechsli/Haptic-Feedback-Robot-Controller---Master-Thesis/Data/frequency_response/ardu_ref_plots/figs/tracking17plot_zoom.jpg

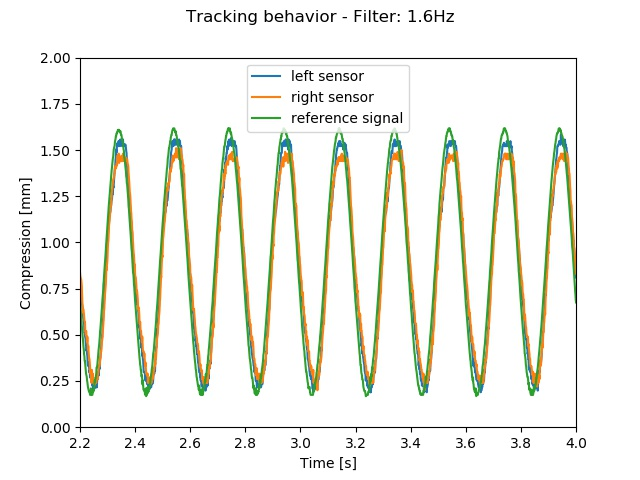
Data/frequency_response/ardu_ref_plots/figs/tracking17plot_zoom.jpg
