roechsli/Haptic-Feedback-Robot-Controller---Master-Thesis/Data/frequency_response/ardu_ref_plots/figs/tracking22plot_zoom.jpg

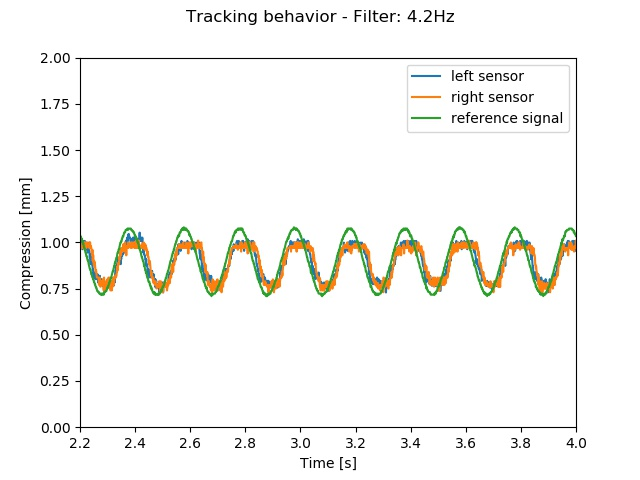
Data/frequency_response/ardu_ref_plots/figs/tracking22plot_zoom.jpg
