roechsli/Haptic-Feedback-Robot-Controller---Master-Thesis/Reports/oechslin_april/Figs/DSC_0335.JPG

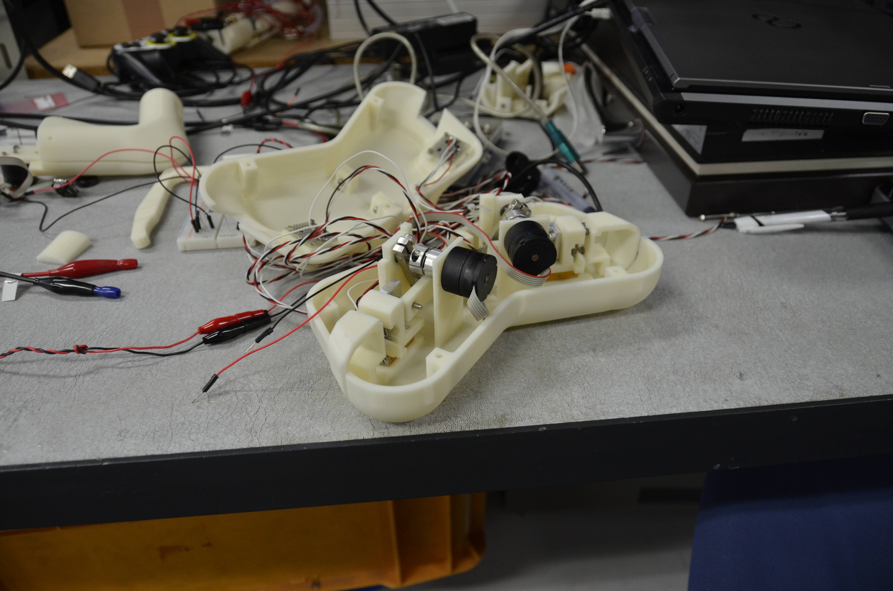
Reports/oechslin_april/Figs/DSC_0335.JPG
