roechsli/Haptic-Feedback-Robot-Controller---Master-Thesis/Reports/oechslin_april/Figs/freq_resp_left_hand_rigid_experim1.png

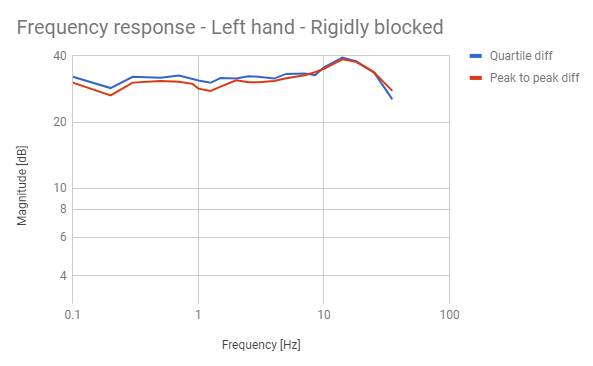
Reports/oechslin_april/Figs/freq_resp_left_hand_rigid_experim1.png
