roechsli/Haptic-Feedback-Robot-Controller---Master-Thesis/Reports/oechslin_july/Figs/topy_playstation_latency_plot.jpg

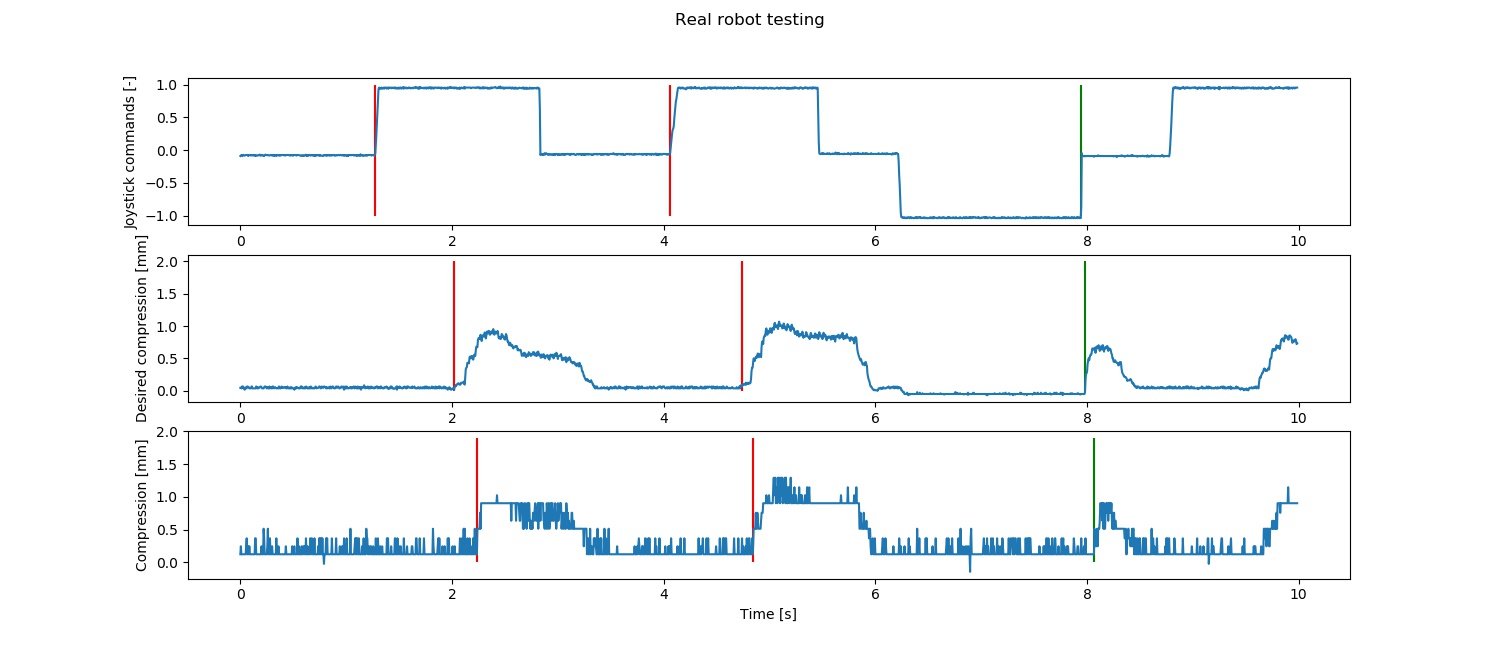
Reports/oechslin_july/Figs/topy_playstation_latency_plot.jpg
