roechsli/Haptic-Feedback-Robot-Controller---Master-Thesis/Reports/oechslin_july/Figs/unity_P_latency_plot.jpg

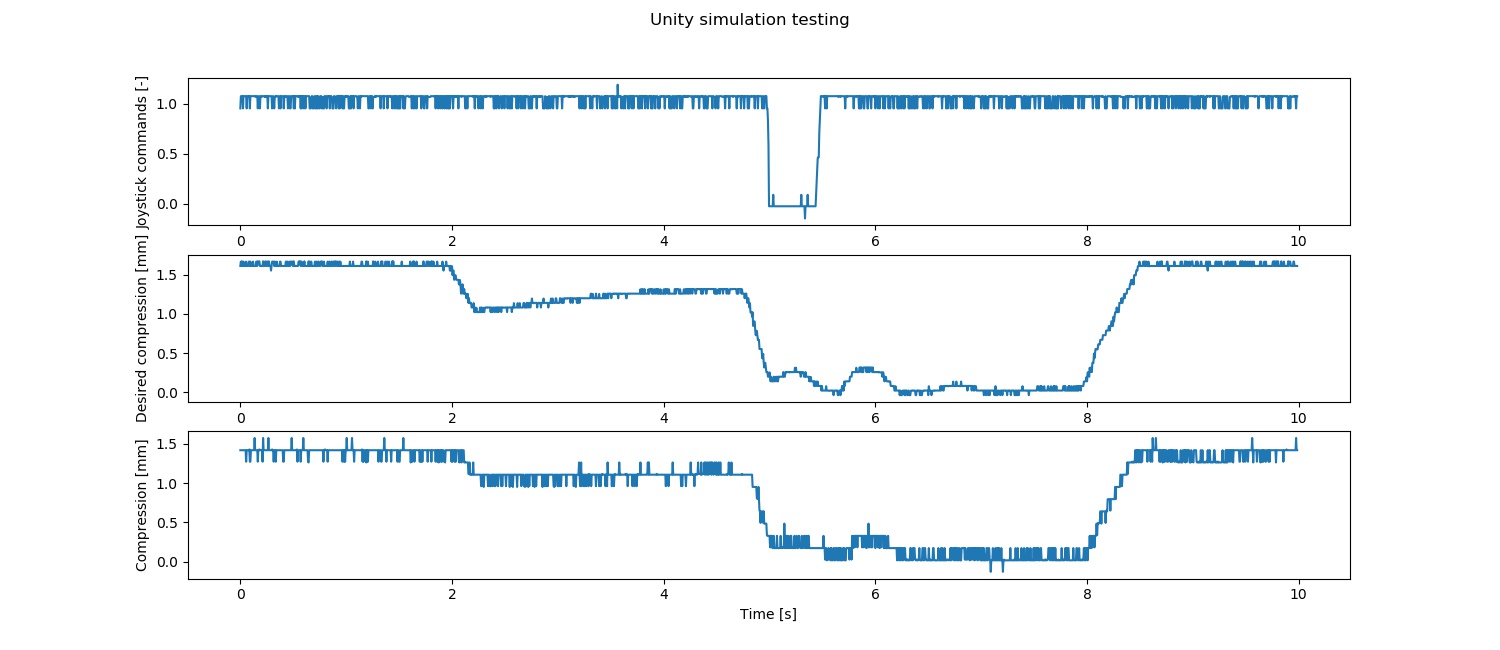
Reports/oechslin_july/Figs/unity_P_latency_plot.jpg
