roechsli/Haptic-Feedback-Robot-Controller---Master-Thesis/Reports/oechslin_july/Figs/unity_PID_latency_plot.jpg

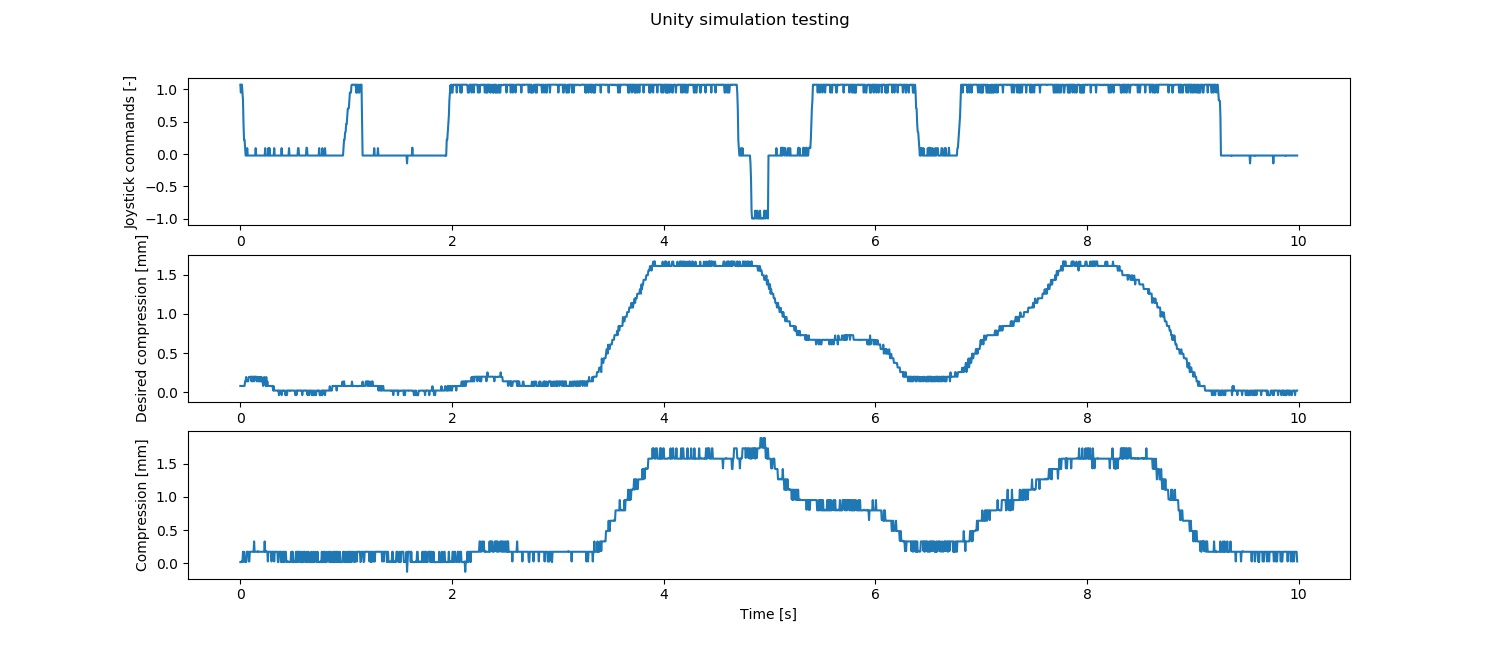
Reports/oechslin_july/Figs/unity_PID_latency_plot.jpg
