roechsli/Haptic-Feedback-Robot-Controller---Master-Thesis/Reports/oechslin_june/Figs/backward_bode_sp_damp300_P02.jpg

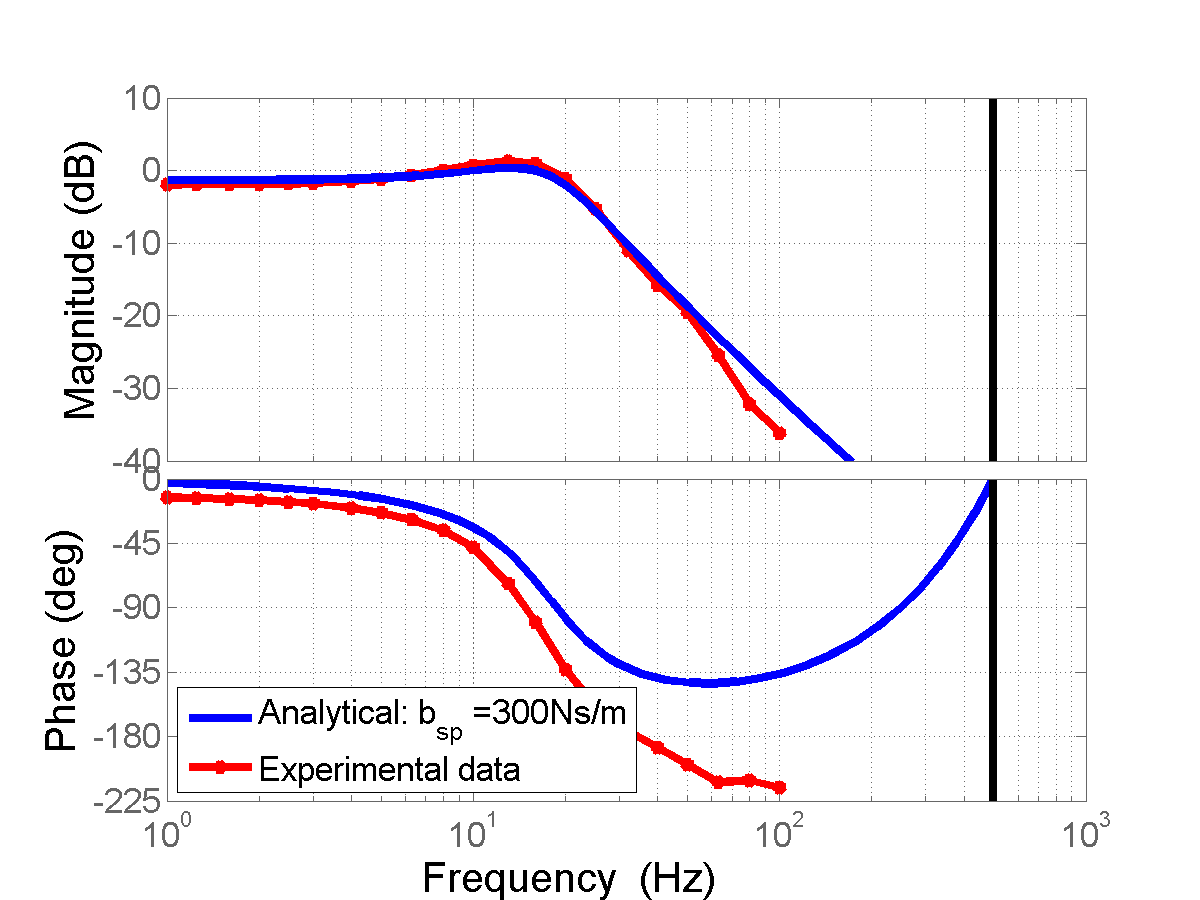
Reports/oechslin_june/Figs/backward_bode_sp_damp300_P02.jpg
