roechsli/Haptic-Feedback-Robot-Controller---Master-Thesis/Reports/oechslin_june/Figs/bode_sp_damp300.jpg

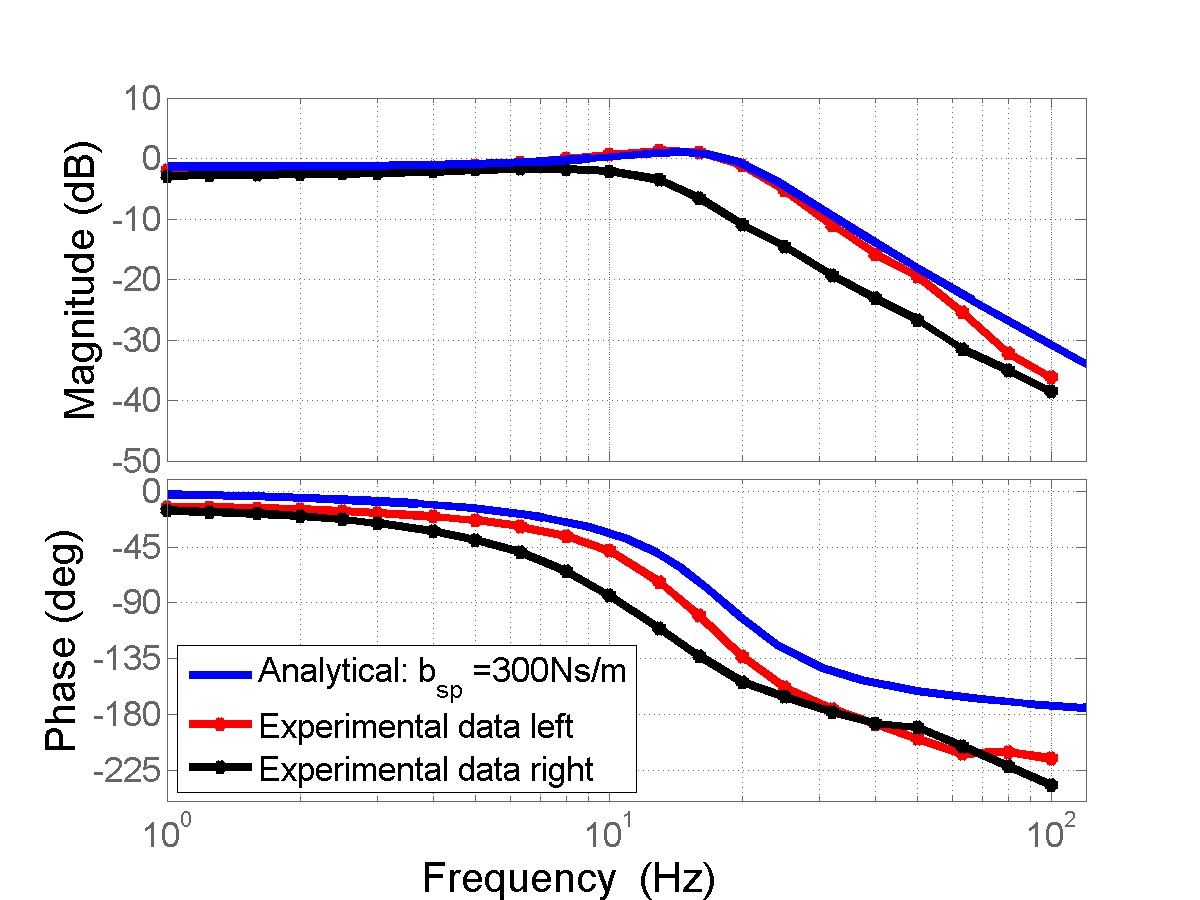
Reports/oechslin_june/Figs/bode_sp_damp300.jpg
