roechsli/Haptic-Feedback-Robot-Controller---Master-Thesis/Data/frequency_response/20180801_pilot_step_tracking2/figs/pilot_tracking_perf3.jpg

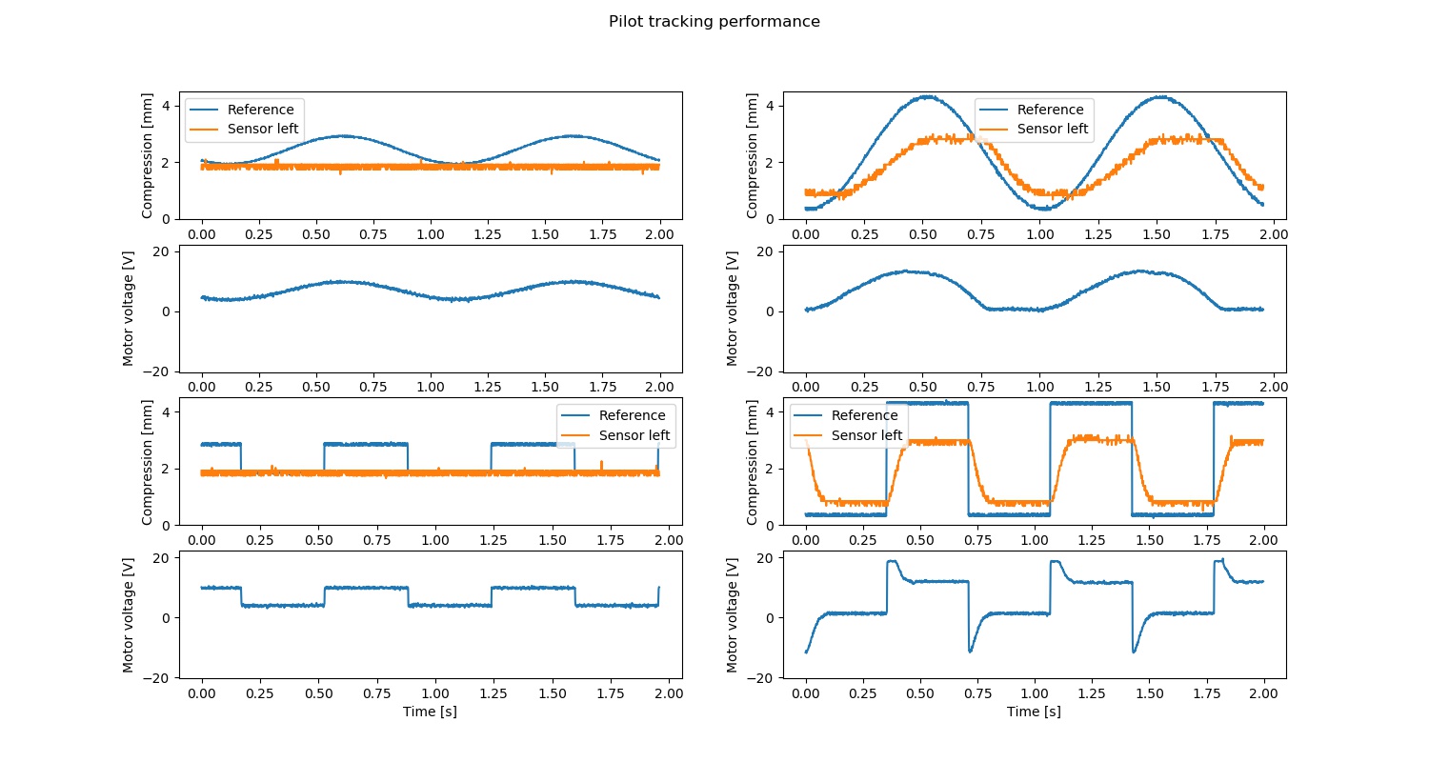
Data/frequency_response/20180801_pilot_step_tracking2/figs/pilot_tracking_perf3.jpg
