roechsli/Haptic-Feedback-Robot-Controller---Master-Thesis/Data/frequency_response/20180801_pilot_step_tracking2/figs/scope_1plot.jpg

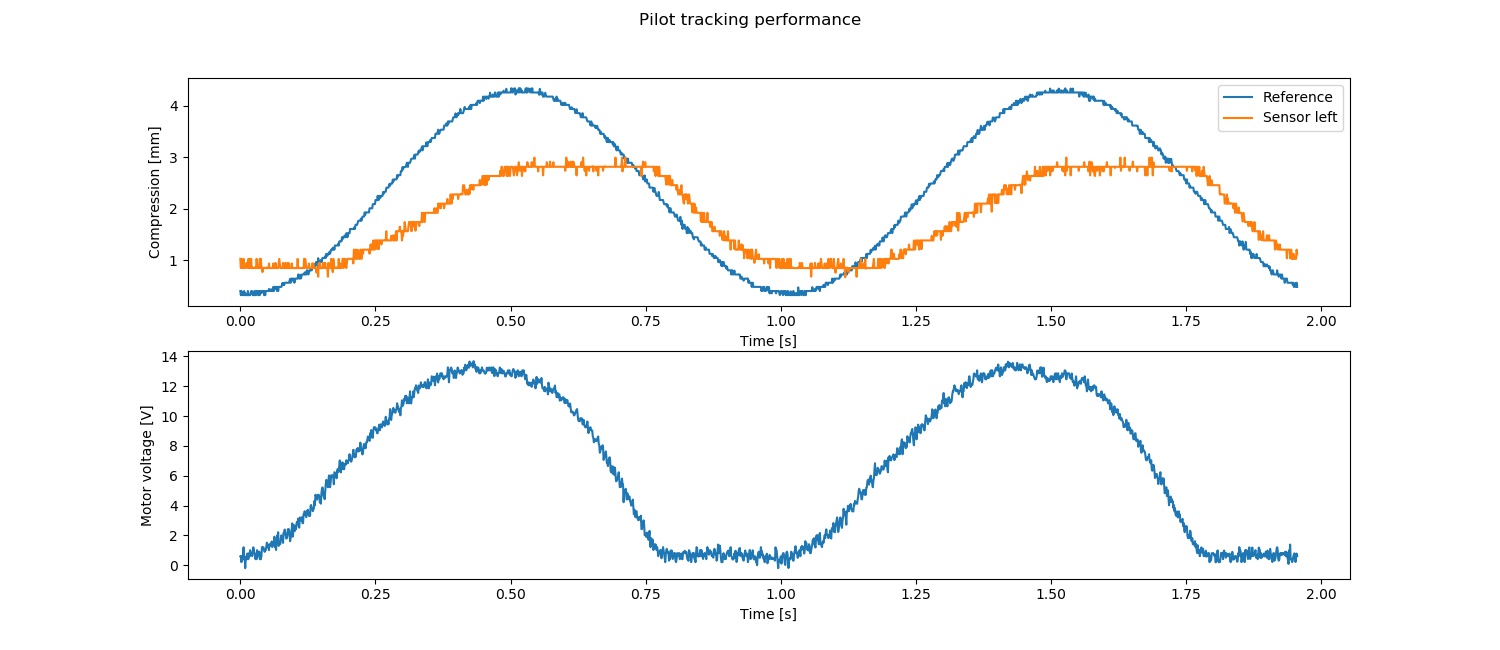
Data/frequency_response/20180801_pilot_step_tracking2/figs/scope_1plot.jpg
