roechsli/Haptic-Feedback-Robot-Controller---Master-Thesis/Data/frequency_response/20180801_pilot_step_tracking/figs/scope_3plot.jpg

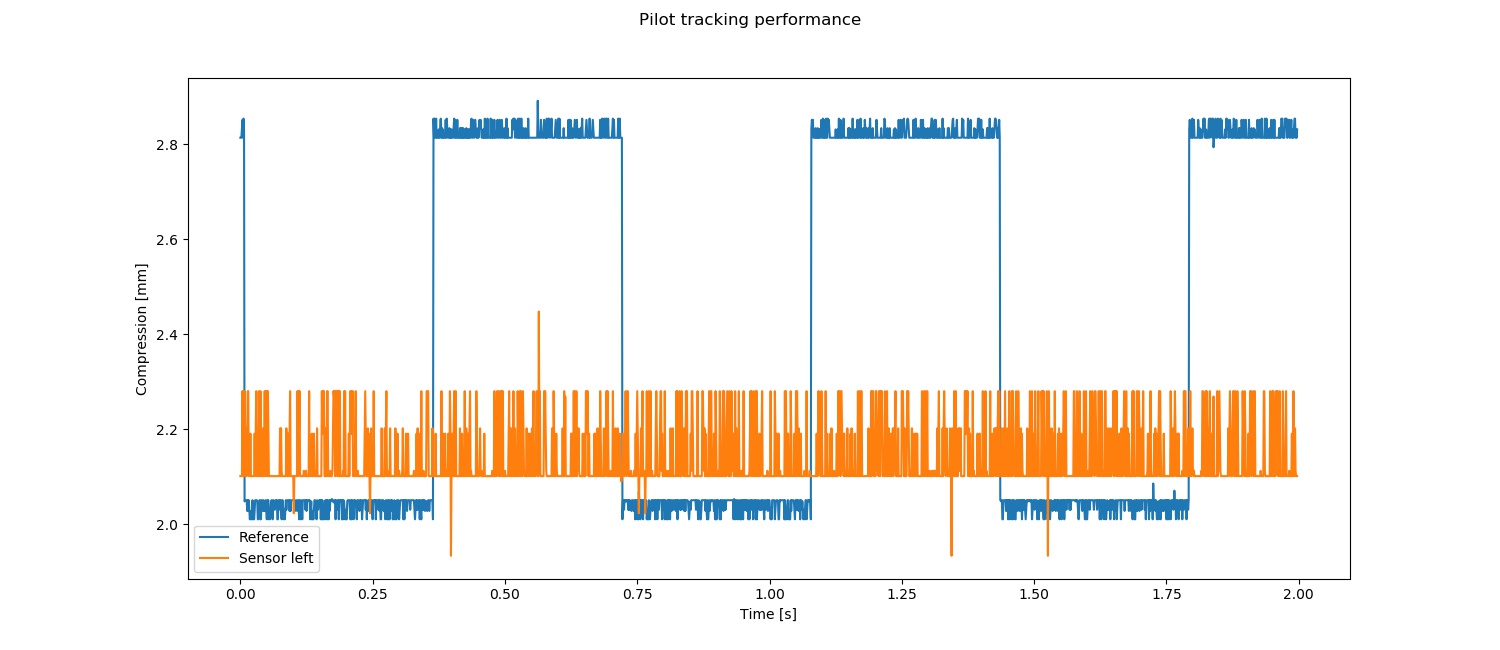
Data/frequency_response/20180801_pilot_step_tracking/figs/scope_3plot.jpg
