roechsli/Haptic-Feedback-Robot-Controller---Master-Thesis/Reports/oechslin_may/Figs/setup.jpg

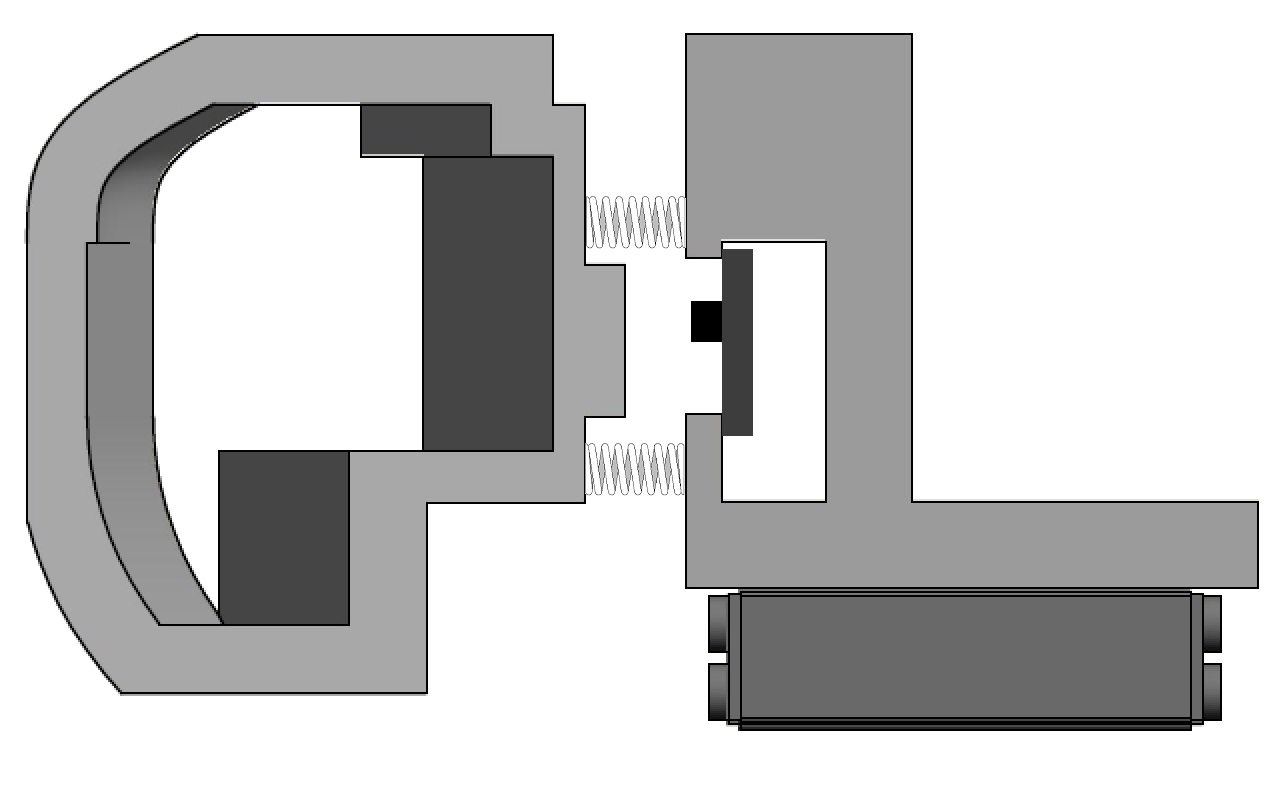
Reports/oechslin_may/Figs/setup.jpg
