roechsli/Haptic-Feedback-Robot-Controller---Master-Thesis/Videos and Photos/yoke_assembled.JPG

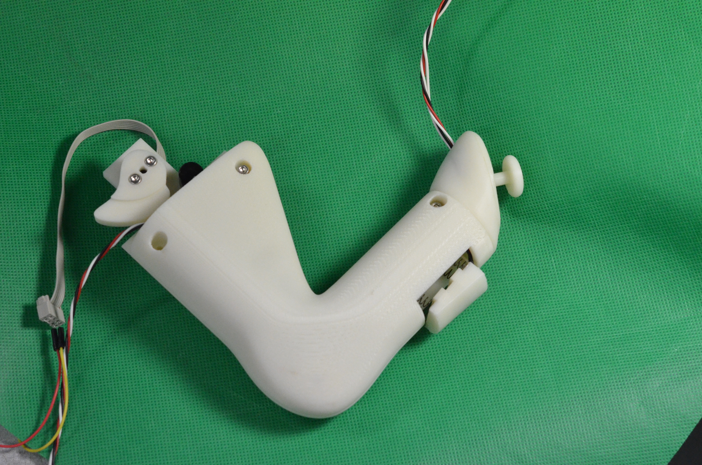
Videos and Photos/yoke_assembled.JPG
