roechsli/Haptic-Feedback-Robot-Controller---Master-Thesis/Data/PID_quality/20180626_init_pid_measure1/oscilloscope plots/scope_13.csv

x-axis | 1 | 2
second | Volt | Volt
-282.8000E-03 | +3.0000000E+00 | +3.2010050E+00
-282.5500E-03 | +2.9899497E+00 | +3.2412060E+00
-282.3000E-03 | +2.9597990E+00 | +3.2412060E+00
-282.0500E-03 | +2.9597990E+00 | +3.1080402E+00
-281.8000E-03 | +2.9597990E+00 | +3.1608040E+00
-281.5500E-03 | +2.9597990E+00 | +3.2412060E+00
-281.3000E-03 | +2.9497487E+00 | +3.2412060E+00
-281.0500E-03 | +2.9497487E+00 | +3.1206030E+00
-280.8000E-03 | +2.9321608E+00 | +3.1608040E+00
-280.5500E-03 | +2.9195980E+00 | +3.2412060E+00
-280.3000E-03 | +2.8919598E+00 | +3.2412060E+00
-280.0500E-03 | +2.9195980E+00 | +3.1206030E+00
-279.8000E-03 | +2.9195980E+00 | +3.1206030E+00
-279.5500E-03 | +2.8919598E+00 | +3.2110553E+00
-279.3000E-03 | +2.8919598E+00 | +3.2688442E+00
-279.0500E-03 | +2.8793970E+00 | +3.1206030E+00
-278.8000E-03 | +2.8517588E+00 | +3.1206030E+00
-278.5500E-03 | +2.8793970E+00 | +3.2010050E+00
-278.3000E-03 | +2.8517588E+00 | +3.2688442E+00
-278.0500E-03 | +2.8517588E+00 | +3.1080402E+00
-277.8000E-03 | +2.8391960E+00 | +3.1206030E+00
-277.5500E-03 | +2.8391960E+00 | +3.1708543E+00
-277.3000E-03 | +2.8391960E+00 | +3.2814070E+00
-277.0500E-03 | +2.8391960E+00 | +3.1206030E+00
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
