roechsli/Haptic-Feedback-Robot-Controller---Master-Thesis/Data/PID_quality/20180626_init_pid_measure1/oscilloscope plots/scope_1.csv

x-axis | 1 | 2
second | Volt | Volt
-249.8000E-03 | +943.1231E-03 | +502.5126E-03
-249.5500E-03 | +963.2236E-03 | +502.5126E-03
-249.3000E-03 | +943.1231E-03 | +502.5126E-03
-249.0500E-03 | +963.2236E-03 | +491.2060E-03
-248.8000E-03 | +943.1231E-03 | +501.2563E-03
-248.5500E-03 | +963.2236E-03 | +502.5126E-03
-248.3000E-03 | +963.2236E-03 | +502.5126E-03
-248.0500E-03 | +963.2236E-03 | +502.5126E-03
-247.8000E-03 | +963.2236E-03 | +502.5126E-03
-247.5500E-03 | +963.2236E-03 | +502.5126E-03
-247.3000E-03 | +943.1231E-03 | +502.5126E-03
-247.0500E-03 | +963.2236E-03 | +502.5126E-03
-246.8000E-03 | +961.9673E-03 | +482.4121E-03
-246.5500E-03 | +963.2236E-03 | +502.5126E-03
-246.3000E-03 | +963.2236E-03 | +502.5126E-03
-246.0500E-03 | +963.2236E-03 | +502.5126E-03
-245.8000E-03 | +963.2236E-03 | +482.4121E-03
-245.5500E-03 | +963.2236E-03 | +502.5126E-03
-245.3000E-03 | +963.2236E-03 | +502.5126E-03
-245.0500E-03 | +963.2236E-03 | +512.5628E-03
-244.8000E-03 | +963.2236E-03 | +502.5126E-03
-244.5500E-03 | +963.2236E-03 | +492.4623E-03
-244.3000E-03 | +963.2236E-03 | +502.5126E-03
-244.0500E-03 | +943.1231E-03 | +512.5628E-03
-243.8000E-03 | +943.1231E-03 | +502.5126E-03
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
