roechsli/Haptic-Feedback-Robot-Controller---Master-Thesis/Data/PID_quality/20180626_init_pid_measure1/oscilloscope plots/scope_10.csv

x-axis | 1 | 2
second | Volt | Volt
-82.80000E-03 | +3.36180904E+00 | +3.24120603E+00
-82.75000E-03 | +3.40201005E+00 | +3.20100502E+00
-82.70000E-03 | +3.40201005E+00 | +3.20100502E+00
-82.65000E-03 | +3.37185929E+00 | +3.22864321E+00
-82.60000E-03 | +3.37185929E+00 | +3.24120603E+00
-82.55000E-03 | +3.38944723E+00 | +3.24120603E+00
-82.50000E-03 | +3.40201005E+00 | +3.24120603E+00
-82.45000E-03 | +3.37185929E+00 | +3.28140703E+00
-82.40000E-03 | +3.36180904E+00 | +3.28140703E+00
-82.35000E-03 | +3.40201005E+00 | +3.28140703E+00
-82.30000E-03 | +3.36180904E+00 | +3.30904522E+00
-82.25000E-03 | +3.36180904E+00 | +3.32160804E+00
-82.20000E-03 | +3.36180904E+00 | +3.34924623E+00
-82.15000E-03 | +3.38944723E+00 | +3.36180904E+00
-82.10000E-03 | +3.37185929E+00 | +3.36180904E+00
-82.05000E-03 | +3.40201005E+00 | +3.37185929E+00
-82.00000E-03 | +3.36180904E+00 | +3.36180904E+00
-81.95000E-03 | +3.37185929E+00 | +3.34924623E+00
-81.90000E-03 | +3.37185929E+00 | +3.32160804E+00
-81.85000E-03 | +3.40201005E+00 | +3.28140703E+00
-81.80000E-03 | +3.40201005E+00 | +3.24120603E+00
-81.75000E-03 | +3.38944723E+00 | +3.24120603E+00
-81.70000E-03 | +3.40201005E+00 | +3.20100502E+00
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
