roechsli/Haptic-Feedback-Robot-Controller---Master-Thesis/Data/PID_quality/20180626_init_pid_measure1/oscilloscope plots/scope_12.csv

x-axis | 1 | 2
second | Volt | Volt
-82.80000E-03 | +4.17587938E+00 | +4.12562813E+00
-82.75000E-03 | +4.17587938E+00 | +4.12562813E+00
-82.70000E-03 | +4.16582913E+00 | +4.12562813E+00
-82.65000E-03 | +4.16582913E+00 | +4.12562813E+00
-82.60000E-03 | +4.17587938E+00 | +4.13567838E+00
-82.55000E-03 | +4.20603014E+00 | +4.12562813E+00
-82.50000E-03 | +4.19346732E+00 | +4.08542712E+00
-82.45000E-03 | +4.20603014E+00 | +4.05527637E+00
-82.40000E-03 | +4.16582913E+00 | +4.01507537E+00
-82.35000E-03 | +4.16582913E+00 | +4.04522612E+00
-82.30000E-03 | +4.19346732E+00 | +4.04522612E+00
-82.25000E-03 | +4.16582913E+00 | +4.04522612E+00
-82.20000E-03 | +4.19346732E+00 | +4.05527637E+00
-82.15000E-03 | +4.19346732E+00 | +4.04522612E+00
-82.10000E-03 | +4.19346732E+00 | +4.05527637E+00
-82.05000E-03 | +4.16582913E+00 | +4.08542712E+00
-82.00000E-03 | +4.16582913E+00 | +4.11306531E+00
-81.95000E-03 | +4.19346732E+00 | +4.09547738E+00
-81.90000E-03 | +4.16582913E+00 | +4.11306531E+00
-81.85000E-03 | +4.19346732E+00 | +4.12562813E+00
-81.80000E-03 | +4.17587938E+00 | +4.12562813E+00
-81.75000E-03 | +4.16582913E+00 | +4.12562813E+00
-81.70000E-03 | +4.19346732E+00 | +4.12562813E+00
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
