roechsli/Haptic-Feedback-Robot-Controller---Master-Thesis/Data/hysteresis_testing/test1_20180730/Figure_1.jpeg

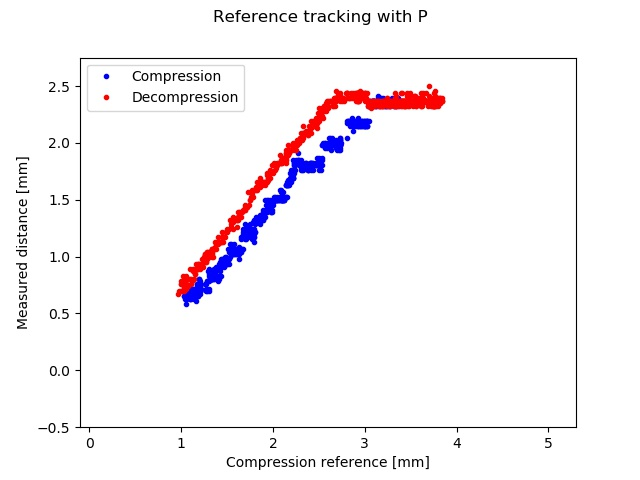
Data/hysteresis_testing/test1_20180730/Figure_1.jpeg
