roechsli/Haptic-Feedback-Robot-Controller---Master-Thesis/Data/hysteresis_testing/test1_20180730/pilot_hysteresis_plot_P15_test2.jpeg

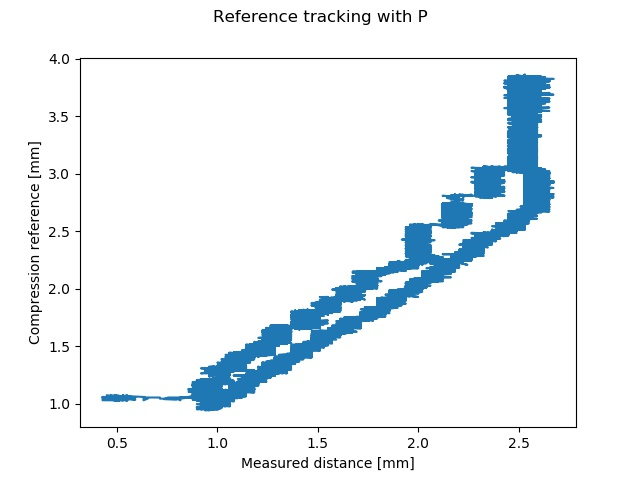
Data/hysteresis_testing/test1_20180730/pilot_hysteresis_plot_P15_test2.jpeg
