roechsli/Haptic-Feedback-Robot-Controller---Master-Thesis/Data/hysteresis_testing/test1_20180730/ref_tracking_plot.jpeg

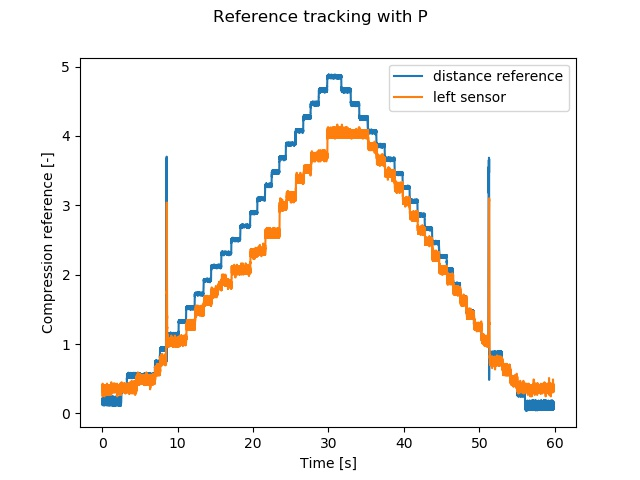
Data/hysteresis_testing/test1_20180730/ref_tracking_plot.jpeg
