roechsli/Haptic-Feedback-Robot-Controller---Master-Thesis/Data/hysteresis_testing/test2_20180731/pilot_hysteresis_P5.jpeg

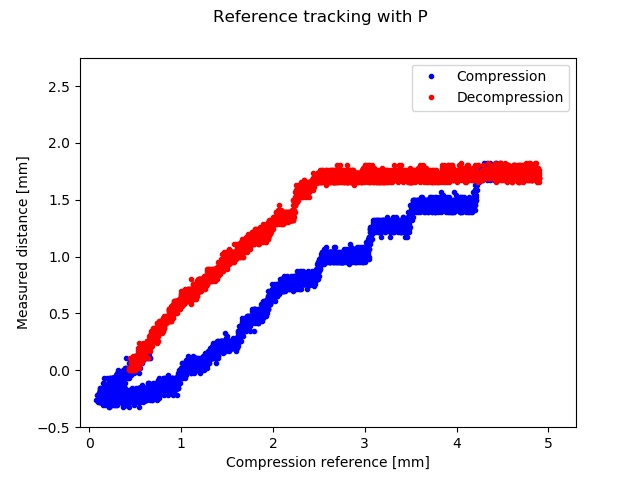
Data/hysteresis_testing/test2_20180731/pilot_hysteresis_P5.jpeg
