roechsli/Haptic-Feedback-Robot-Controller---Master-Thesis/Data/linearity_testing/v3_sensor_characteristics.png

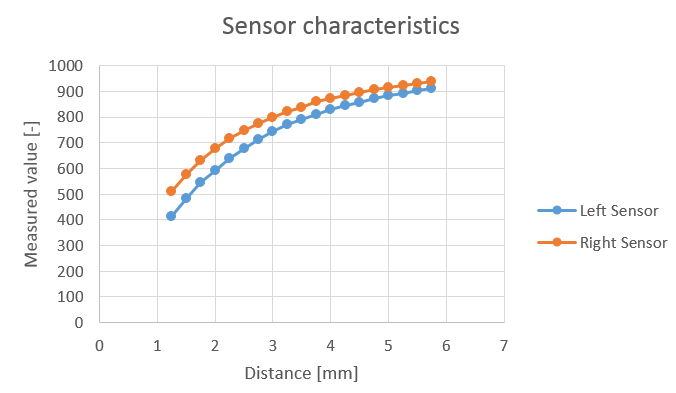
Data/linearity_testing/v3_sensor_characteristics.png
