roechsli/Haptic-Feedback-Robot-Controller---Master-Thesis/Data/PID_quality/20180626_init_pid_measure1/bode_all_combinedKP02.png

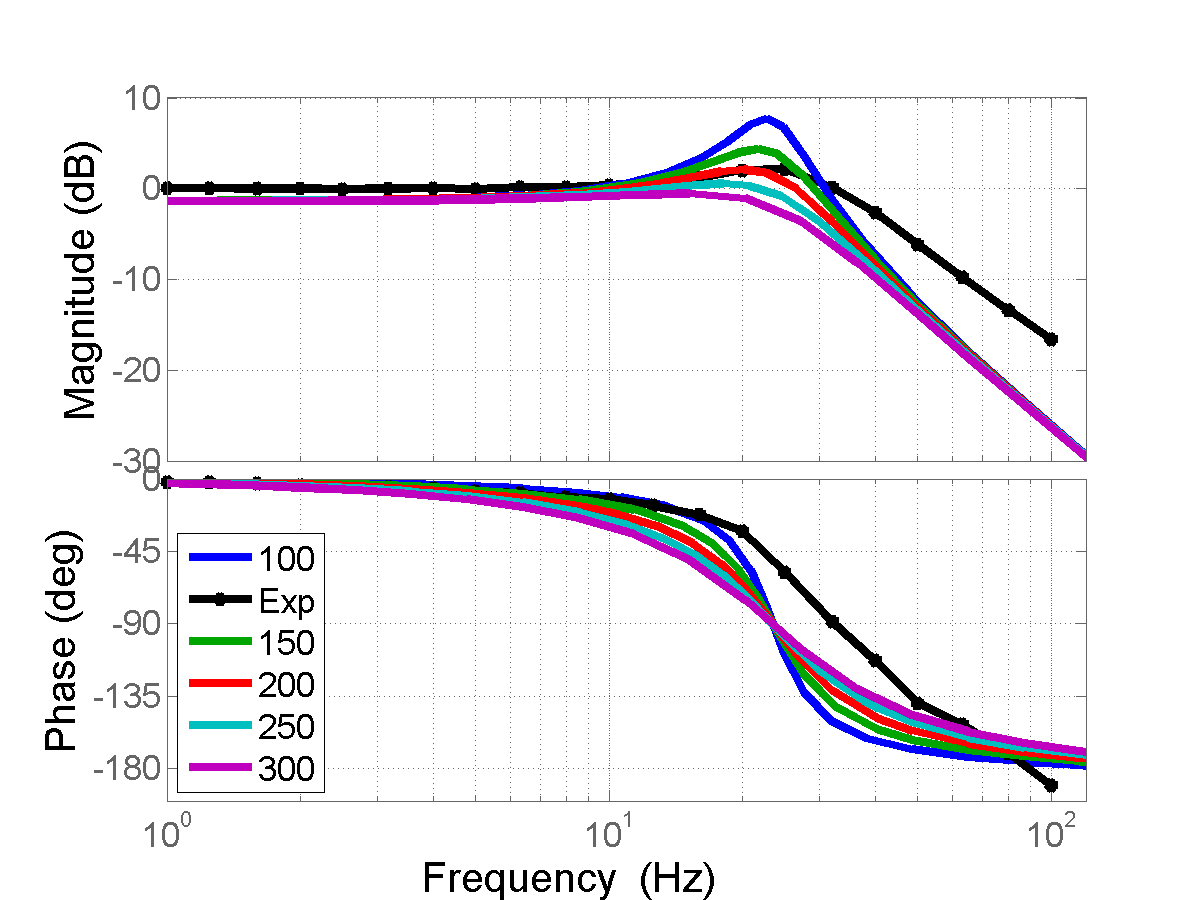
Data/PID_quality/20180626_init_pid_measure1/bode_all_combinedKP02.png
