roechsli/Haptic-Feedback-Robot-Controller---Master-Thesis/Data/real_controller_testing/playstation_ctrller/osc_data/topy_playstation_latency_plot.jpg

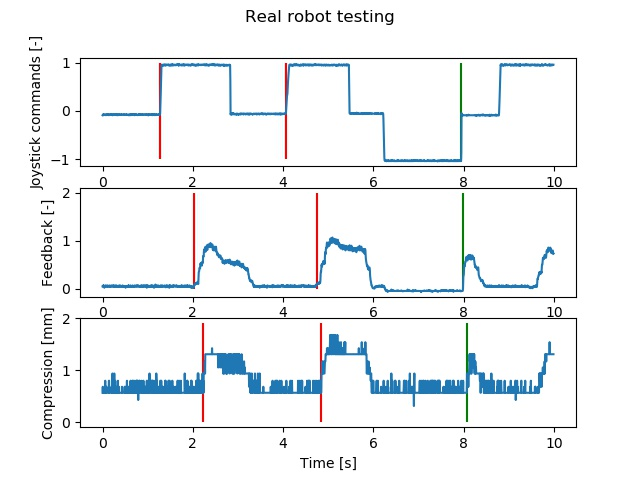
Data/real_controller_testing/playstation_ctrller/osc_data/topy_playstation_latency_plot.jpg
