roechsli/Haptic-Feedback-Robot-Controller---Master-Thesis/Data/unity_controller_testing/pilot_ctrller/figs/a4_latency_plot_hand_P.jpg

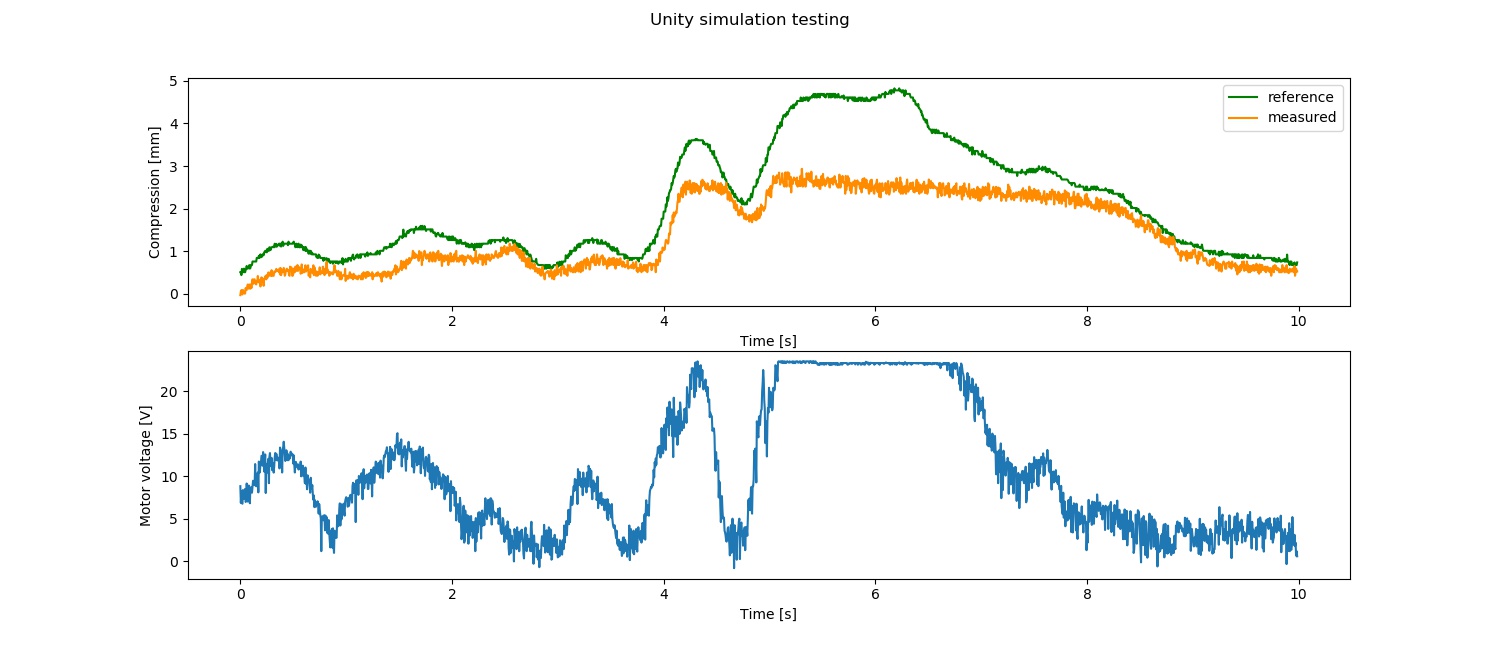
Data/unity_controller_testing/pilot_ctrller/figs/a4_latency_plot_hand_P.jpg
