roechsli/Haptic-Feedback-Robot-Controller---Master-Thesis/Data/unity_controller_testing/pilot_ctrller/figs/a7fake.jpg

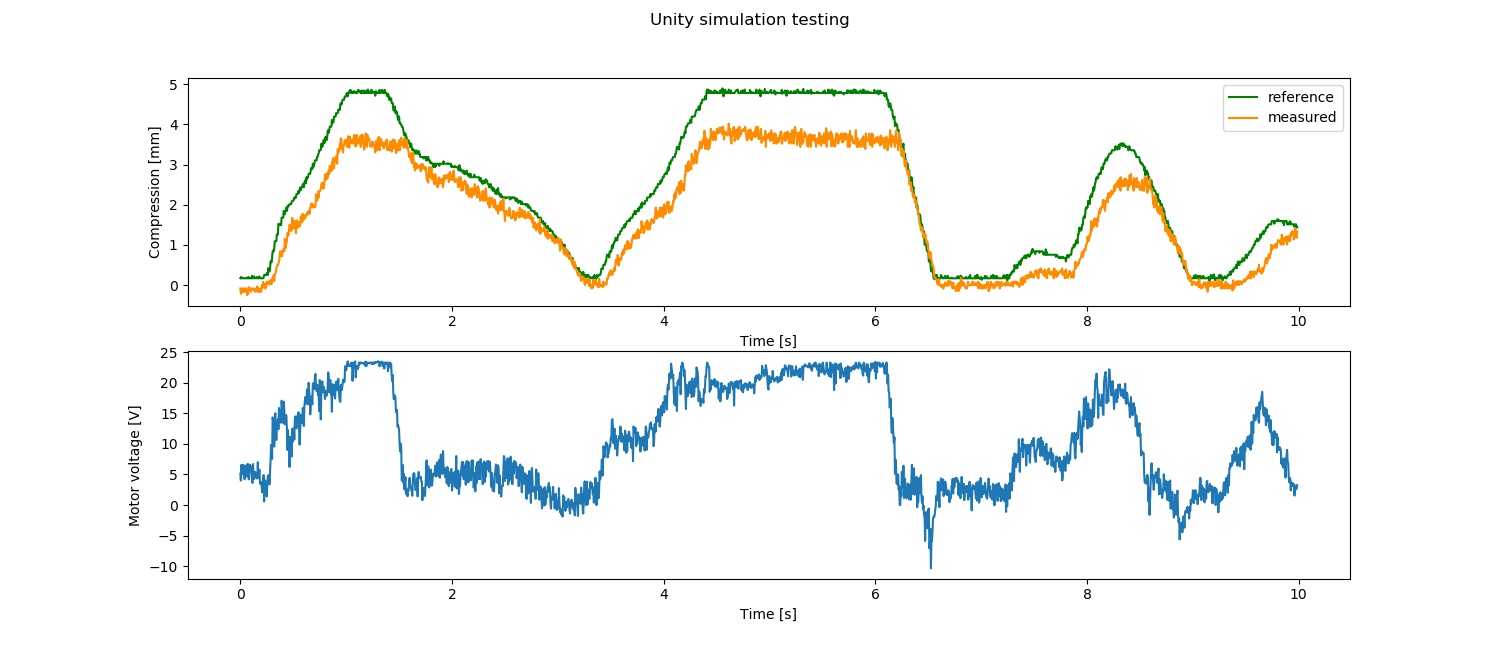
Data/unity_controller_testing/pilot_ctrller/figs/a7fake.jpg
