roechsli/Haptic-Feedback-Robot-Controller---Master-Thesis/Data/unity_controller_testing/pilot_ctrller/figs/cclamp/pilot_unity_scope_1_latency_plot_cclamp_P.jpg

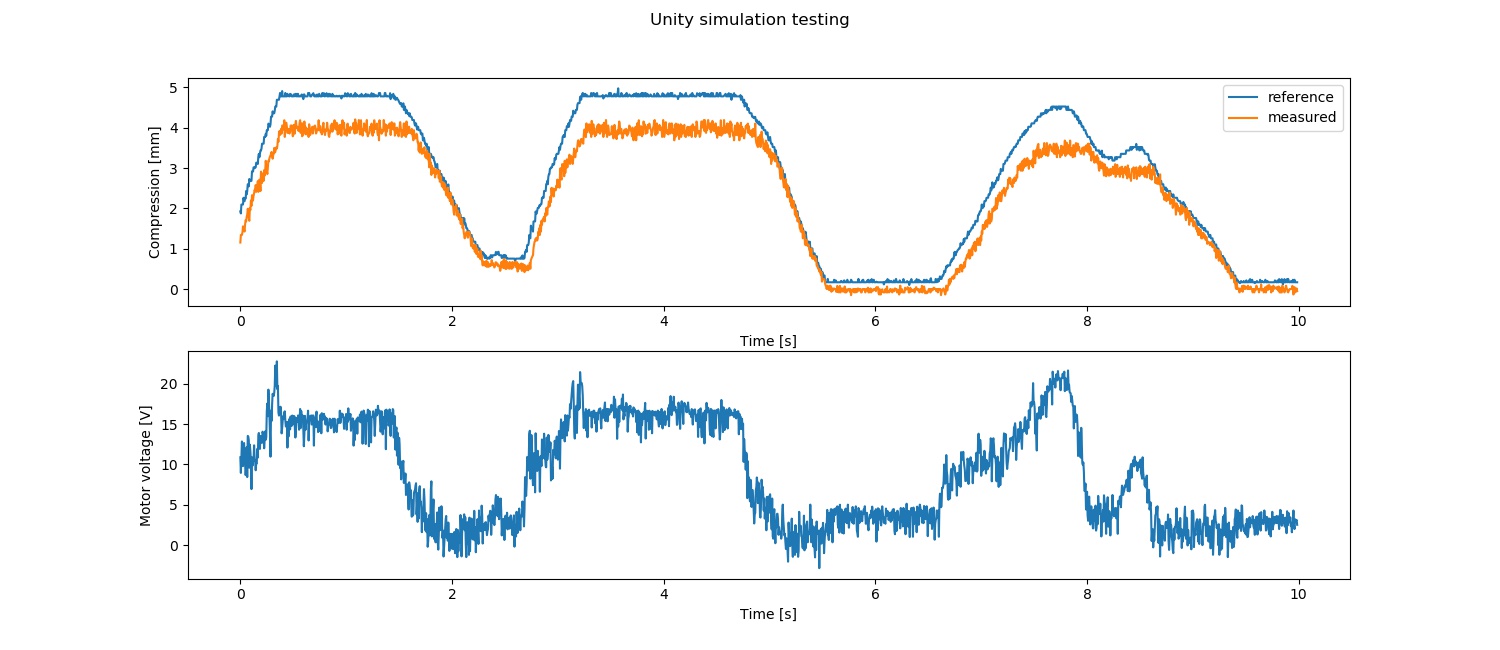
Data/unity_controller_testing/pilot_ctrller/figs/cclamp/pilot_unity_scope_1_latency_plot_cclamp_P.jpg
