roechsli/Haptic-Feedback-Robot-Controller---Master-Thesis/Data/unity_controller_testing/pilot_ctrller/figs/cclamp/scope_0_latency_plot.jpg

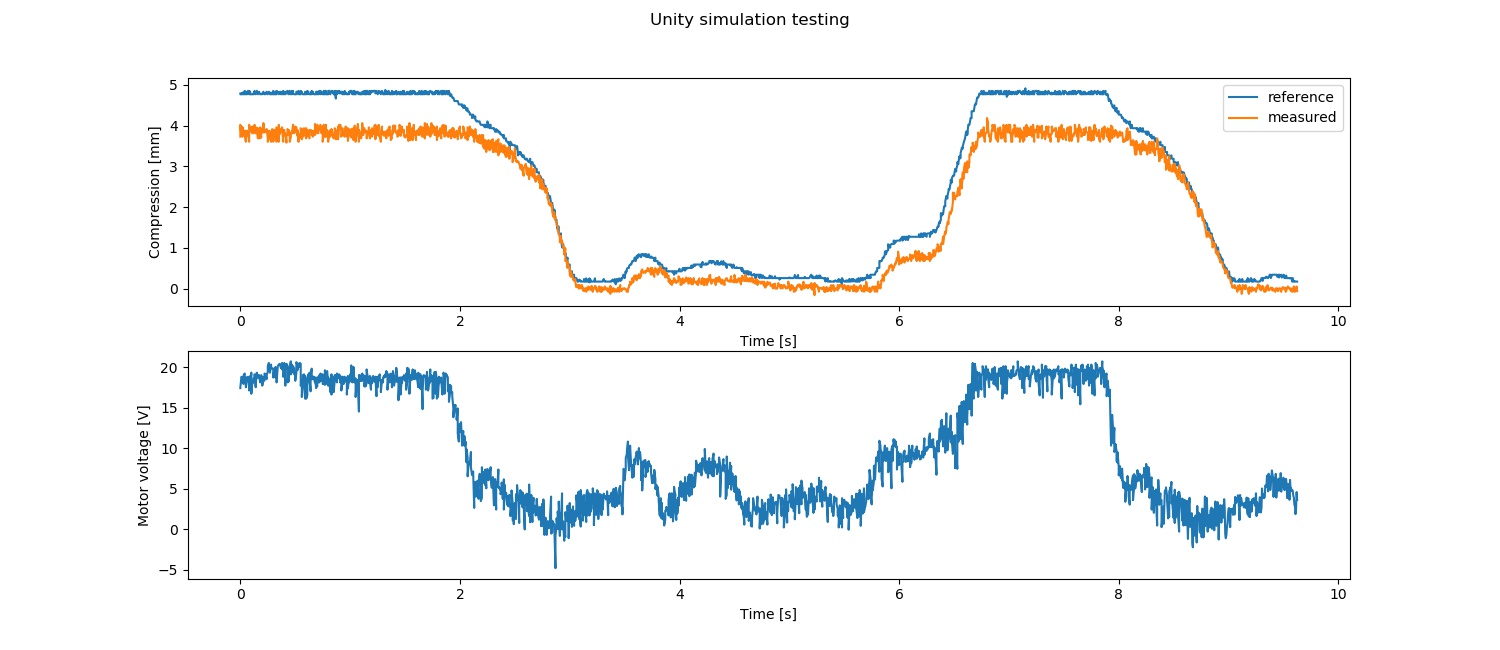
Data/unity_controller_testing/pilot_ctrller/figs/cclamp/scope_0_latency_plot.jpg
