roechsli/Haptic-Feedback-Robot-Controller---Master-Thesis/Data/unity_controller_testing/pilot_ctrller/figs/scope_1_latency_plot.jpg

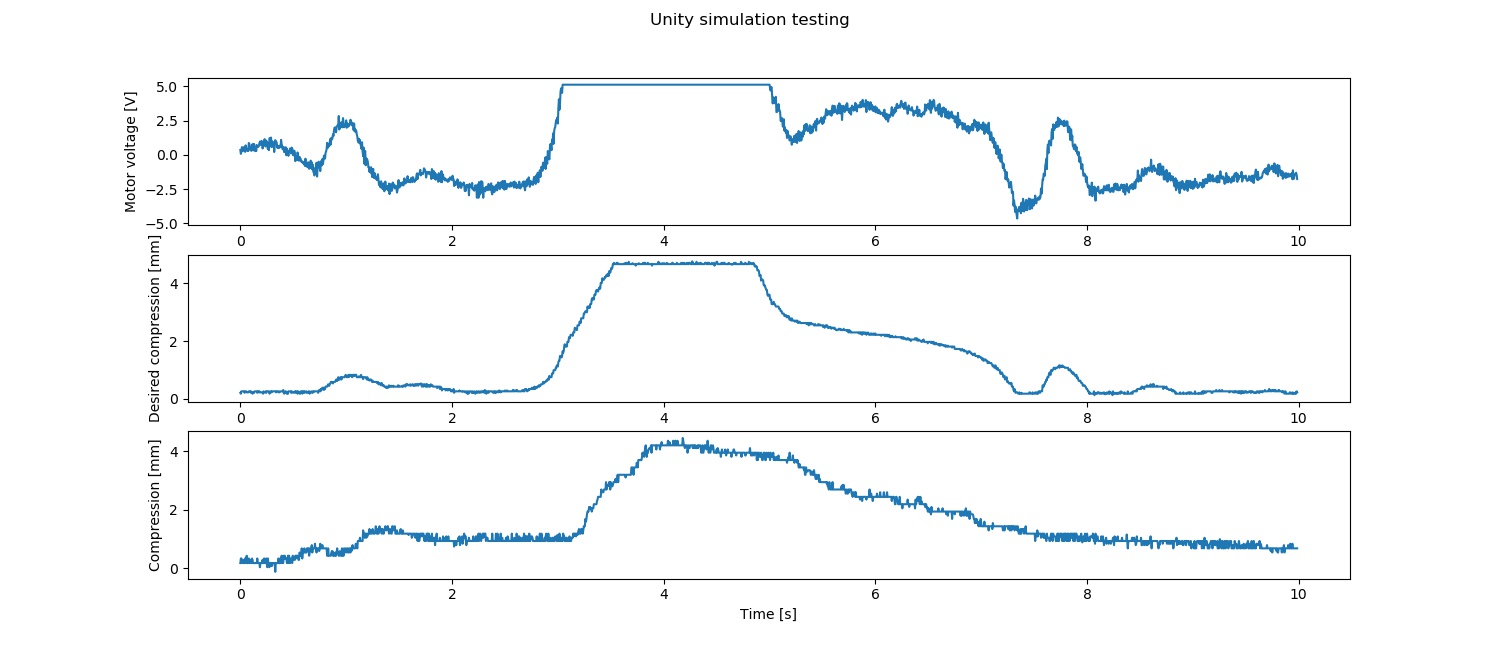
Data/unity_controller_testing/pilot_ctrller/figs/scope_1_latency_plot.jpg
