roechsli/Haptic-Feedback-Robot-Controller---Master-Thesis/Data/unity_controller_testing/playstation_ctrller/figs/b1_latency_plot_wall_P.jpg

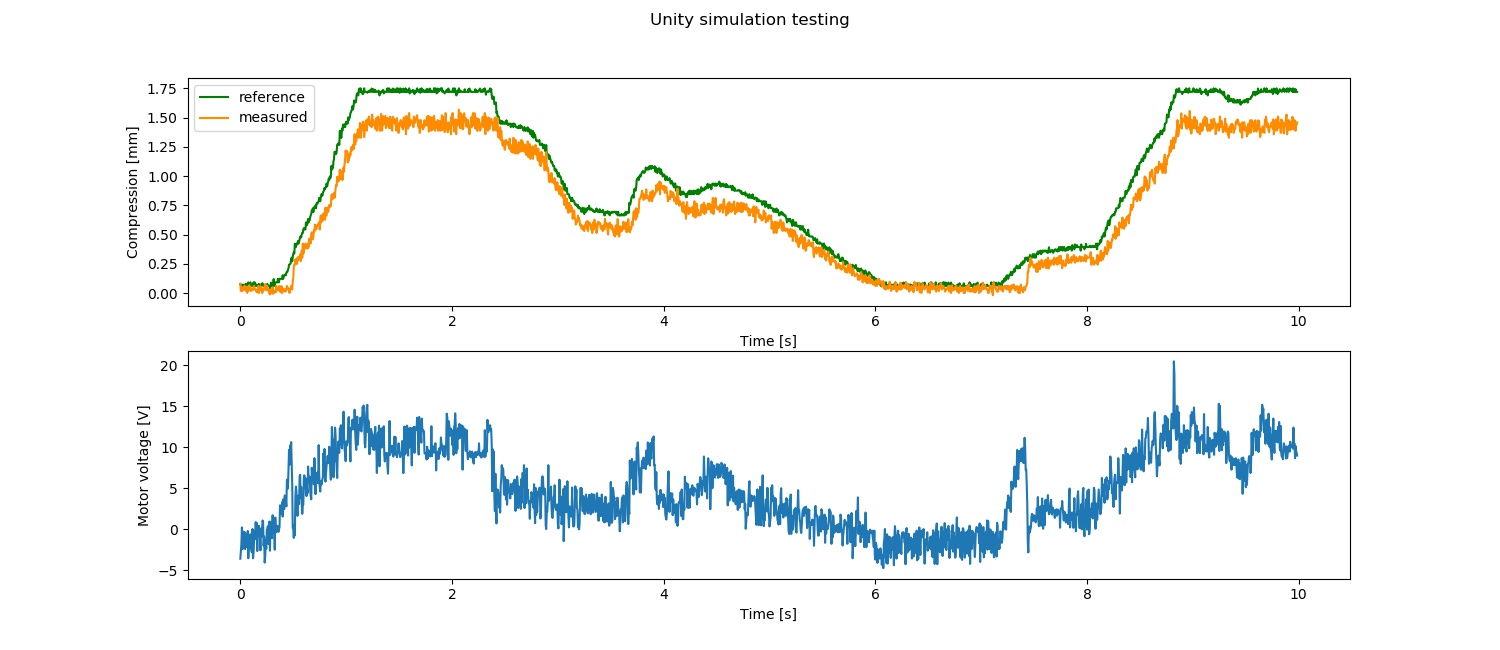
Data/unity_controller_testing/playstation_ctrller/figs/b1_latency_plot_wall_P.jpg
