roechsli/Haptic-Feedback-Robot-Controller---Master-Thesis/Data/unity_controller_testing/playstation_ctrller/figs/b7_latency_plot_wall_PID.jpg

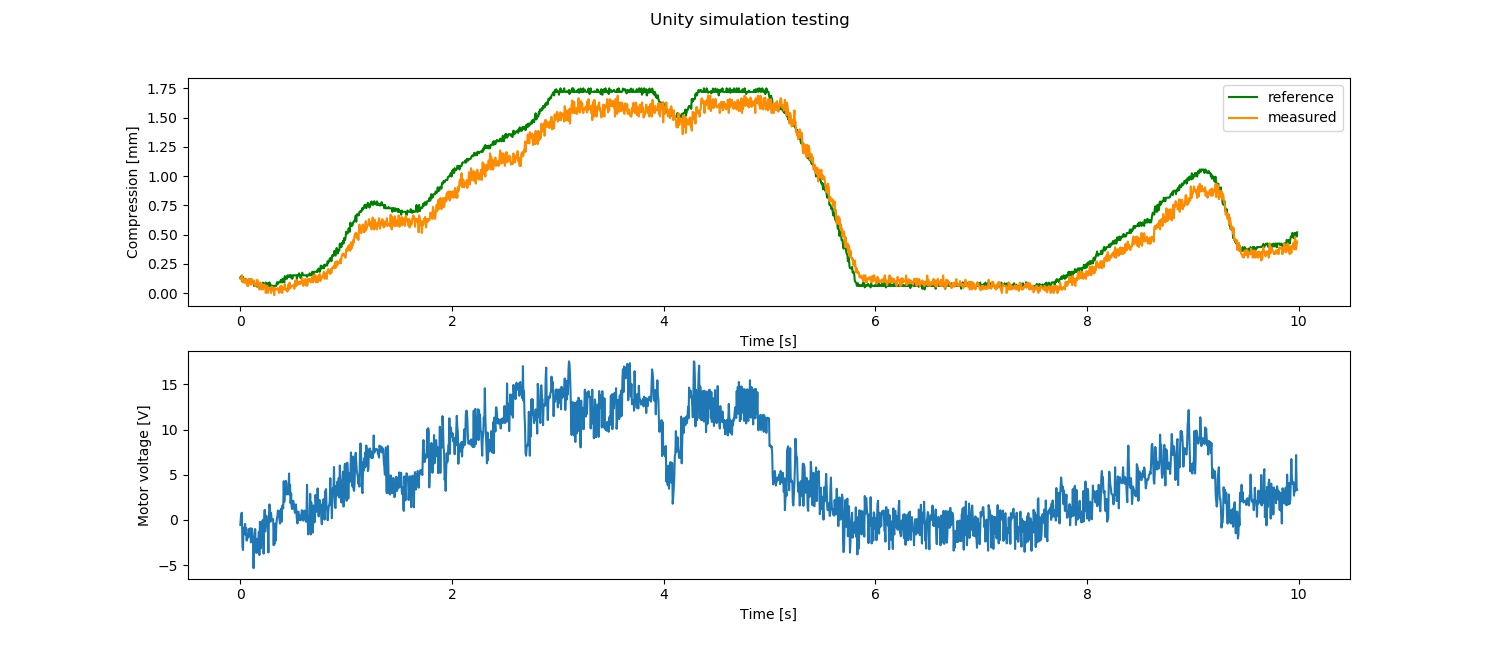
Data/unity_controller_testing/playstation_ctrller/figs/b7_latency_plot_wall_PID.jpg
