roechsli/Haptic-Feedback-Robot-Controller---Master-Thesis/Data/unity_controller_testing/playstation_ctrller/figs/b8_latency_plot_hand_P.jpg

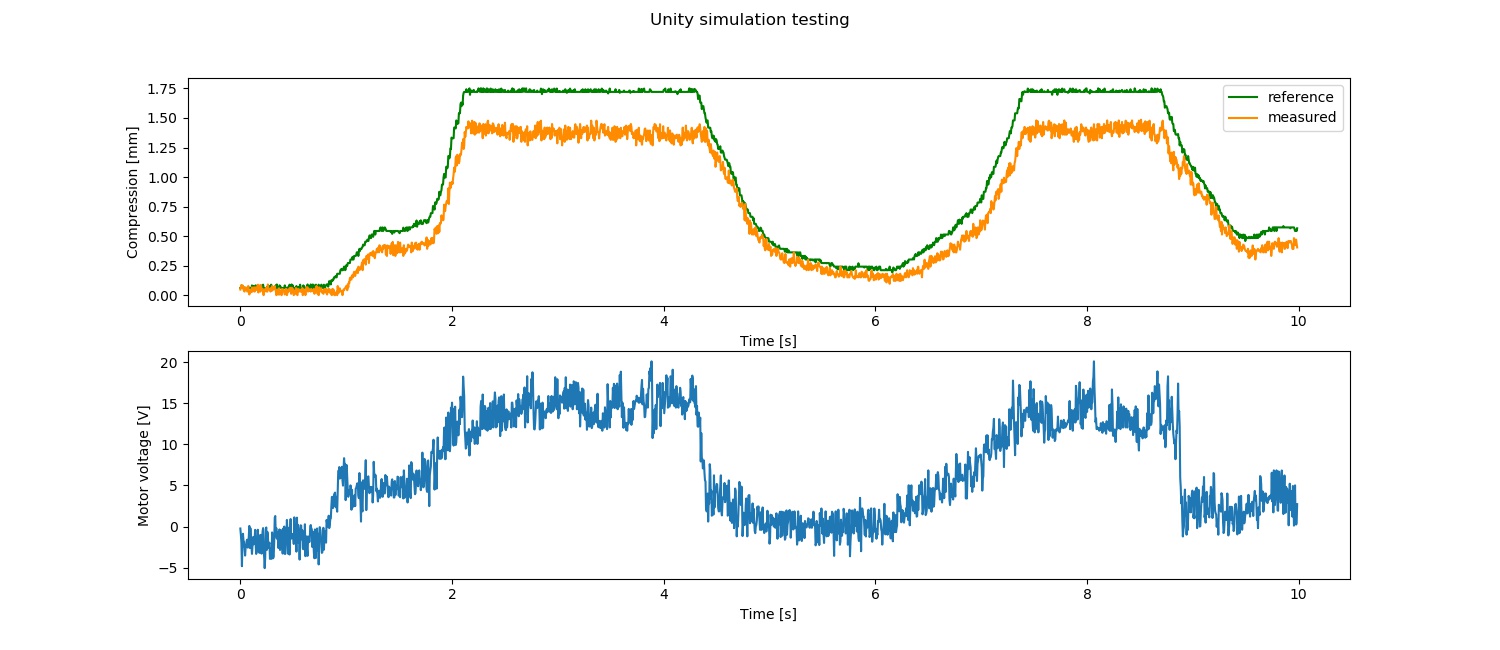
Data/unity_controller_testing/playstation_ctrller/figs/b8_latency_plot_hand_P.jpg
