roechsli/Haptic-Feedback-Robot-Controller---Master-Thesis/Data/unity_controller_testing/playstation_ctrller/figs/b11_latency_plot_hand_PID.jpg

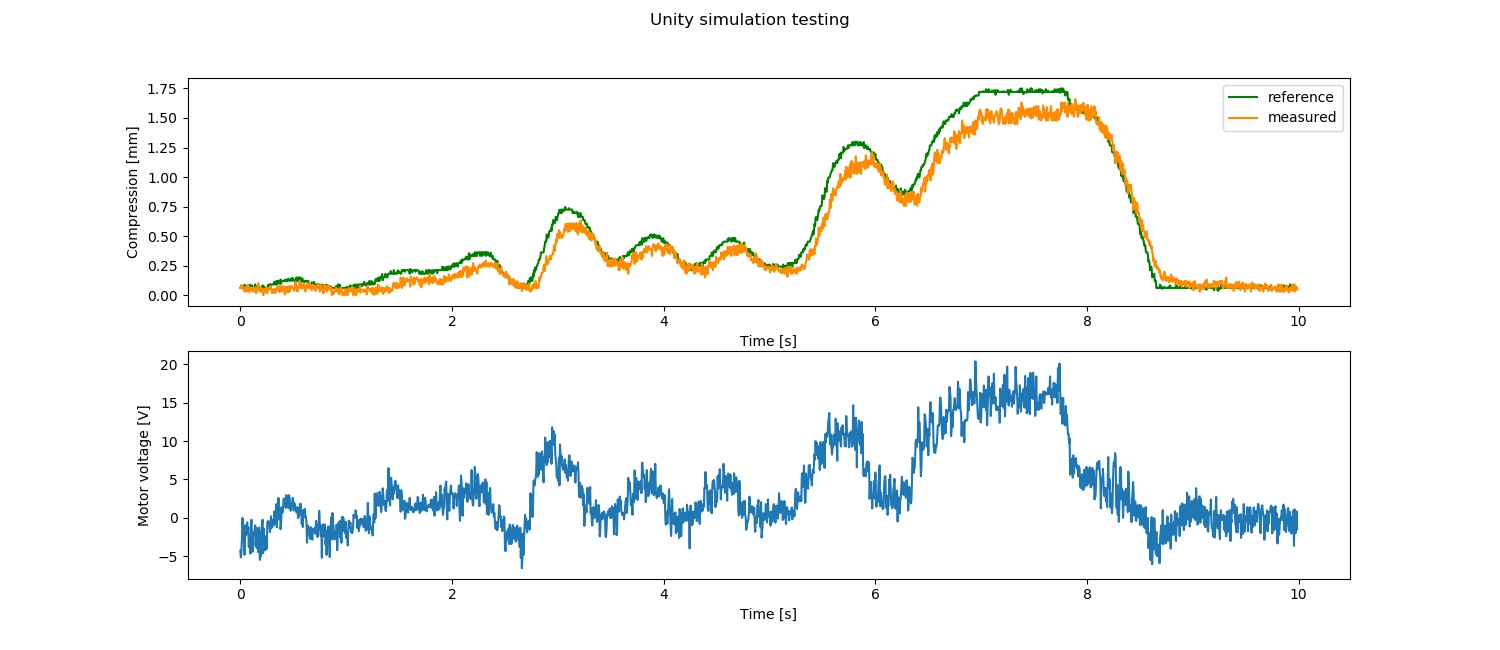
Data/unity_controller_testing/playstation_ctrller/figs/b11_latency_plot_hand_PID.jpg
