roechsli/Haptic-Feedback-Robot-Controller---Master-Thesis/Data/unity_controller_testing/playstation_ctrller/figs/b13_latency_plot.jpg

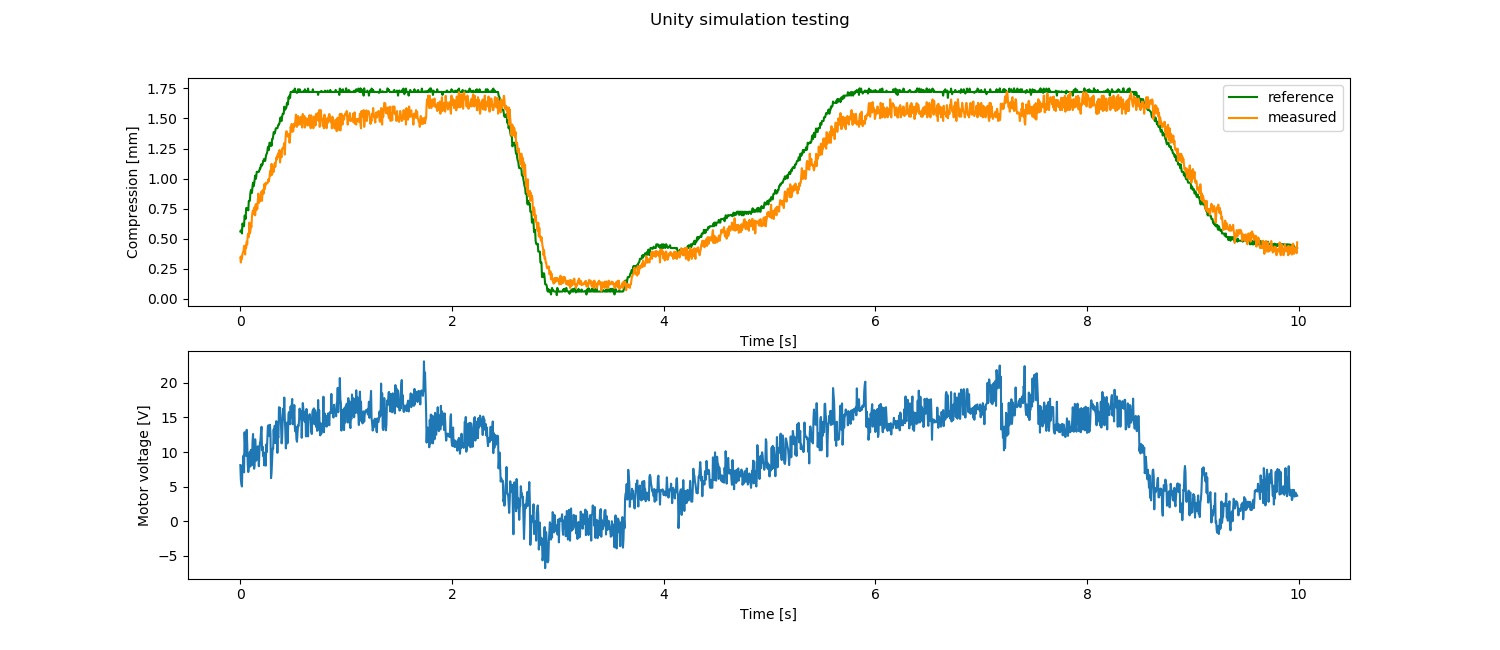
Data/unity_controller_testing/playstation_ctrller/figs/b13_latency_plot.jpg
