roechsli/Haptic-Feedback-Robot-Controller---Master-Thesis/3D designs/Yoke Controller/drawings/yoke_joystick_mount.pdf

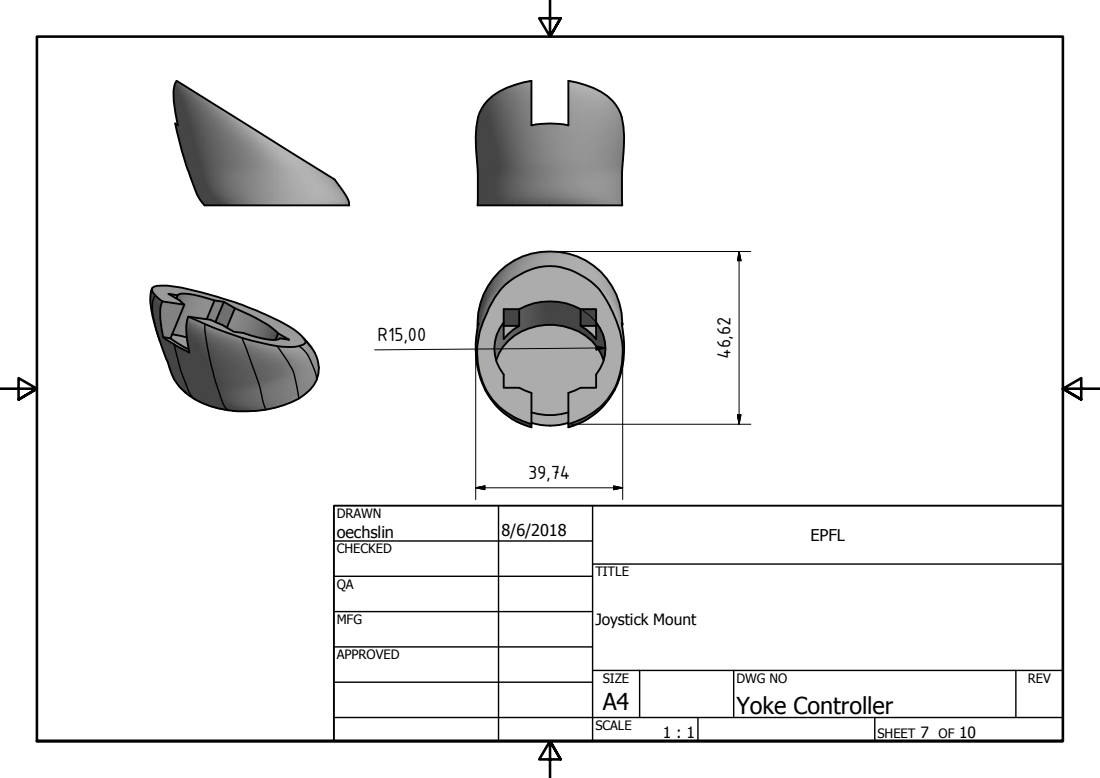
[picture p300: page 1]
Joystick Mount

DRAWN oechslin | 8/6/2018 | EPFL

CHECKED

MFG

APPROVED

SIZE A4 | DWG NO Yoke Controller | REV

SCALE 1 : 1 | | SHEET 7 OF 10
